thereprocase/5680-dock/desk-dock/D8/quick-fit/R5/README.md

# D8 R5: R4 plus a tall underside rail

**18 September 2026.** The printed R4-C pair carried the laptop, but a nudge
tipped it away from the lid rail: the 15-mm short fence cannot hold a 240-mm
lever pivoting on the seat, and the 5-degree lean gives only about 10 mm of
centre-of-gravity margin. R5 raises that fence into a 6-mm underside rail on the **plug-end bracket only**, 64 mm above the seat datum (unleaned z 47..118), keeping
the R2 lower profile, the 2.25-mm running clearance and a 4 x 2 mm lead-in at
the top. The laptop docks along -X from an 18-mm undocked offset, so the rear
rubber-foot strip (x 30..323 docked) sweeps x 30..341: it never reaches the
plug-end bracket (x < 18) but slides through the far-end bracket's x range, so
the far end keeps the R4-C profile without the wall. One wall stops the
rotation. The builder records the docking sweep and asserts the plug-end
clearance. Pair = one R5-C (plug end) + one R4-C (far end); the two R4-C
already printed cover the far end.

Tip receipt (variant C, nominal laptop rotated about the seat front edge toward
the underside side): 2° grazes the lead-in, 4° and beyond the rail carries it.
Everything else is R4: R2 seat, V5 lid-rail move, 6-mm rail, 6-mm base and
brace, fillets and chamfers. `--variant C --base-thickness 4 --tag d9-source`
exports the D9 P4 cradle profile.

Future idea (user, 18 September): make the seat, fence lower profile and
hinge relief a keyed insert so the same two walls and brace serve other
laptops; try a lean of 8 degrees on a bracket pair before changing the dock.
