thereprocase/5680-dock/desk-dock/D9-P5/asa-01-receipts/geometry-review.md

D9 P5 geometry-selected manufacturing review

P5: lean 8 degrees; each cradle end is the R7 frame with a drop-in seat peg
and fence peg locked by one horizontal fan pin (plate 08, 100 % infill,
profile on bed like the cradles). Plate 09 is the M1 cradle end sliced to its
16-mm frame width with the M1 pegs and pin: the cheap 8-degree seat trial,
same pose and profile as the cradle. The plenum, guard, tie and fastener plates
are P4. The lid rail is the only laptop-touching surface left on the frame.

P4 = P3 plus the R5-C underside rail on both outer cradles and three fit
corrections from the printed P2 fit plate: 8.4-mm pin bores (0.2-mm diametral
clearance), key barbs 7.2 mm wide (1.8 mm total interference through the
5.4-mm slot), T tongue 12.1 mm tall (0.6 mm lower). Plate 00 is regenerated so
the new clearances can be trialled before the large parts.

P3 = P2 with the cradle contact taken from the R4-C bracket profile (V5 C seat
relief, lid rail moved 3.5 mm outward, 4-mm base so feet stay coplanar) and a
printable cosmetic edge treatment: fillets on profile corners that run along
each part's print Z (perimeter-only, no overhang), a 0.8-mm chamfer on the
ties' top edges, nothing on bed edges, and every mating zone protected (air
cavity, fan seats, sockets, pin bores, key slots, T joints, guard bars,
laptop contact band). Pins, keys and coupons are byte-identical to P2.

Outer cradle sides: complete broad exterior X face on bed; cavity opens upward.
Inner halves: broad X side on bed; cavity opens upward. Circular fan aperture
opens progressively toward its centre in this orientation. Supports under the
three seam tabs and blind fan sockets are reachable before assembly.
No blanket rejection for downward-facing area is used.
Guards: broad exterior face on bed, bars and spacer towers grow upwards.
Male T ties: broad top on bed; female ties: broad base on bed. The floor-backed
T shoulders carry longitudinal loads. The transverse pin prevents lifting.
Pins: octagonal longitudinal flat on bed; long axes and tension loads in layers.
Keys: broad flat on bed, locking leaves bend in XY. Printed keys are replaceable.
The 8.8-mm transverse bores have two-ended bridge landings and open access.
The selected shell/end-side orientation keeps supported undersides away from
the broad cosmetic outer side. Bed texture is intentional on those faces.
Five walls, six top/bottom layers and 40% gyroid are prototype settings.
Physical contact, load capacity and cooling are untested.
