thereprocase/5680-dock/desk-dock/concept.png

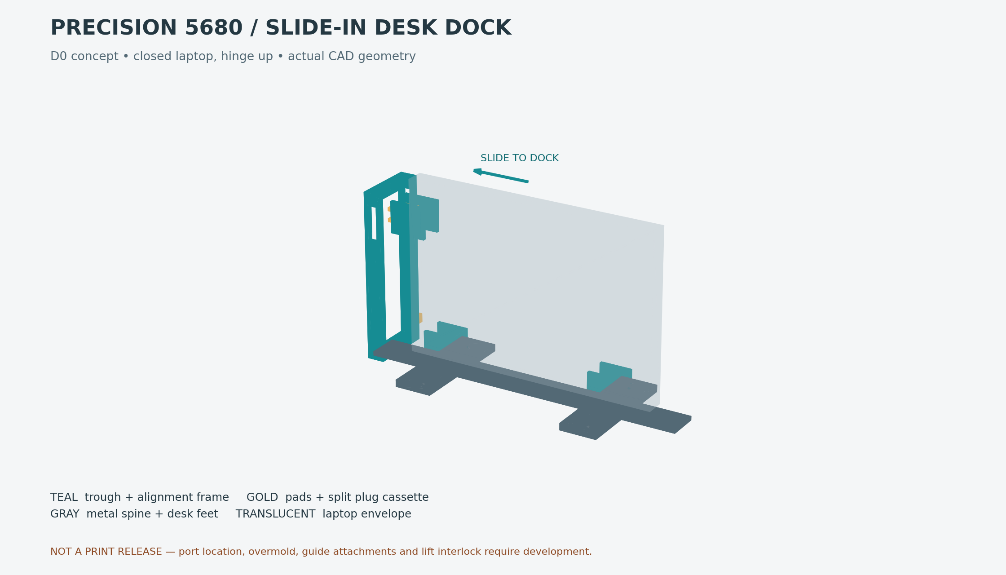
desk-dock/concept.png
