thereprocase/5680-dock/desk-dock/D2/overview.png

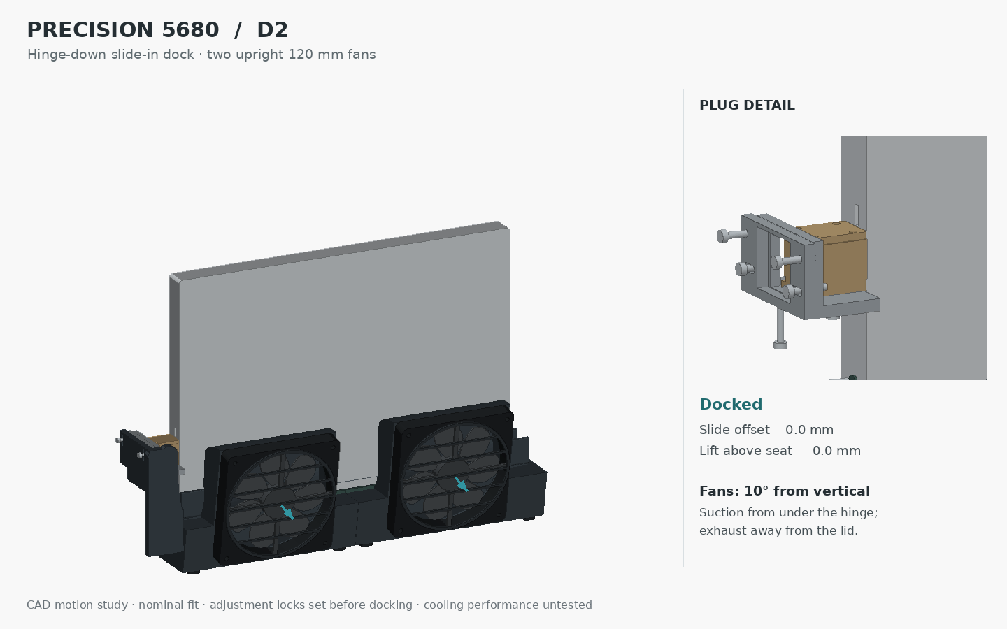
desk-dock/D2/overview.png
