thereprocase/5680-dock/desk-dock/D3/overview.png

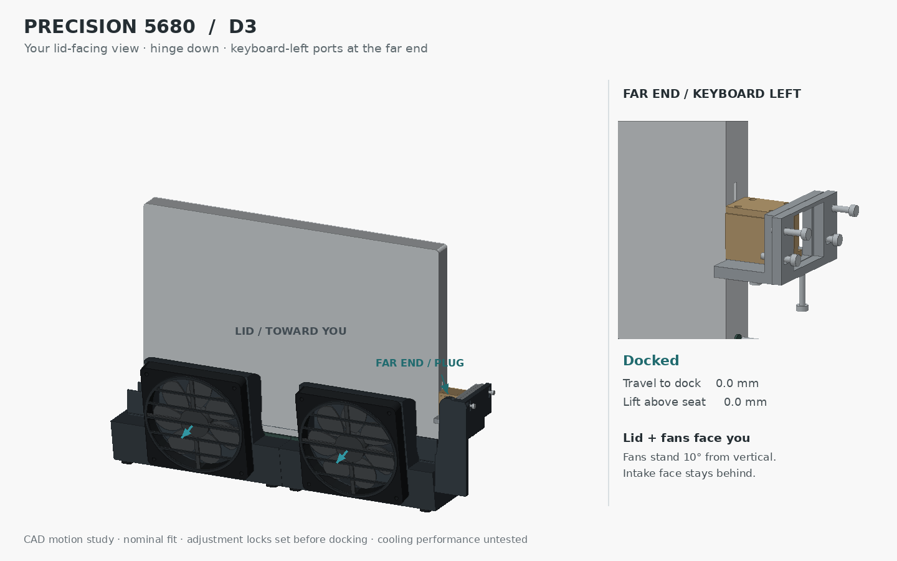
desk-dock/D3/overview.png
