thereprocase/5680-dock/desk-dock/D4/docking-cycle.gif

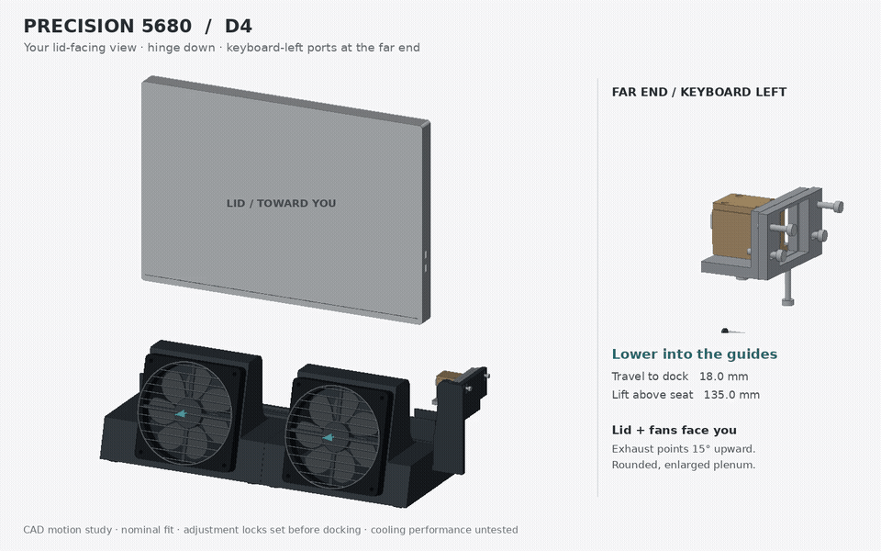
desk-dock/D4/docking-cycle.gif
