thereprocase/5680-dock/desk-dock/D5/docking-cycle.gif

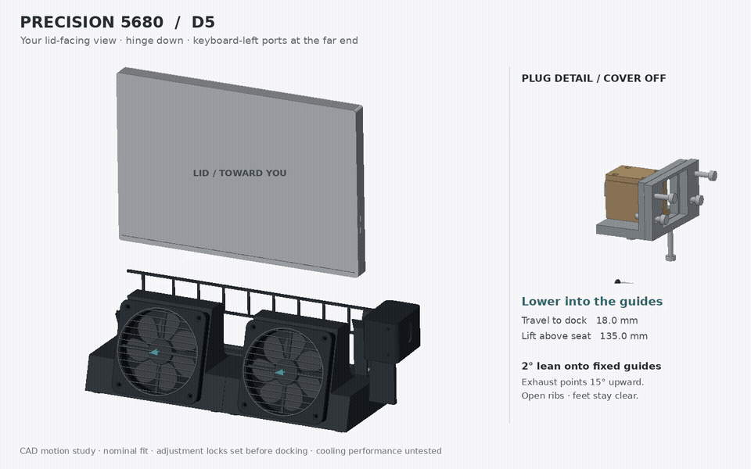
desk-dock/D5/docking-cycle.gif
