thereprocase/5680-dock/desk-dock/D5/profile-detail.png

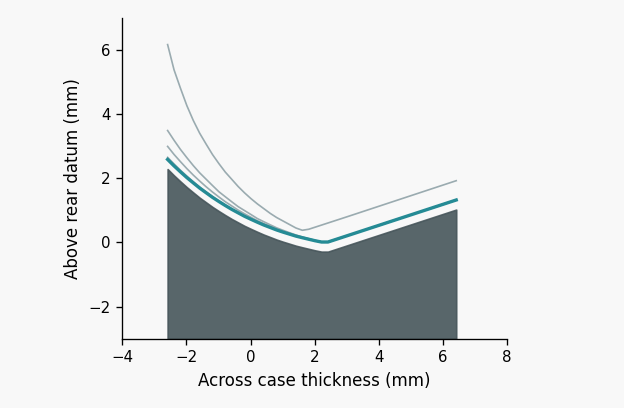
desk-dock/D5/profile-detail.png
