thereprocase/5680-dock/desk-dock/D6/contact-study.png

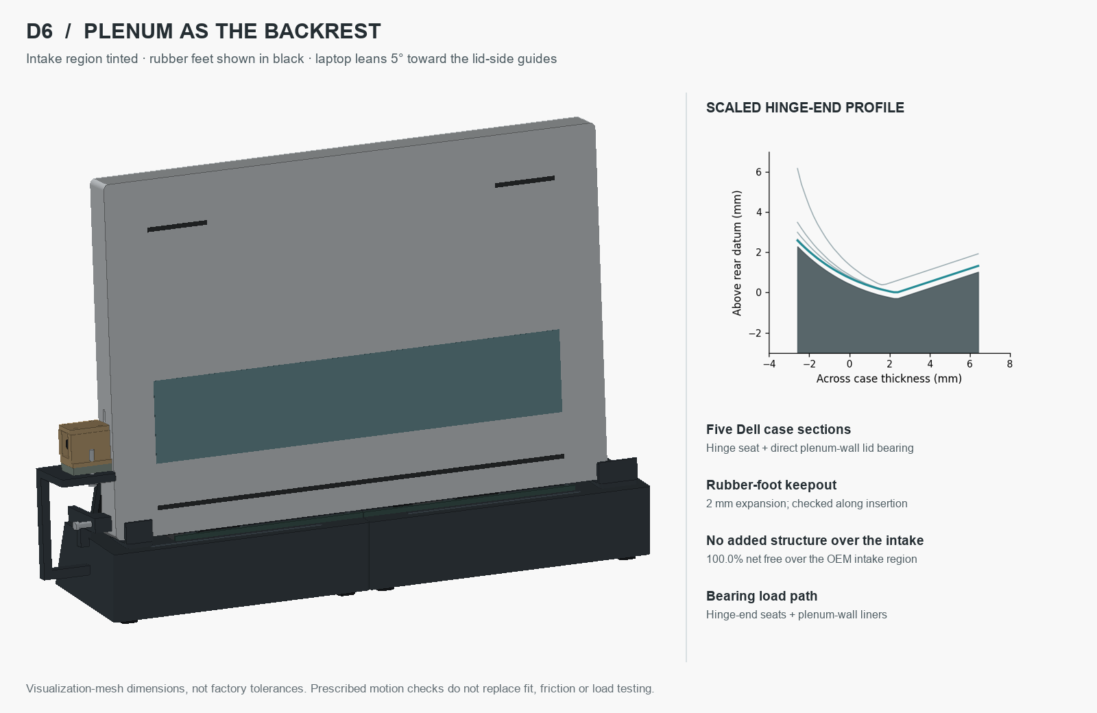
desk-dock/D6/contact-study.png
