thereprocase/5680-dock/desk-dock/D6/docking-cycle.gif

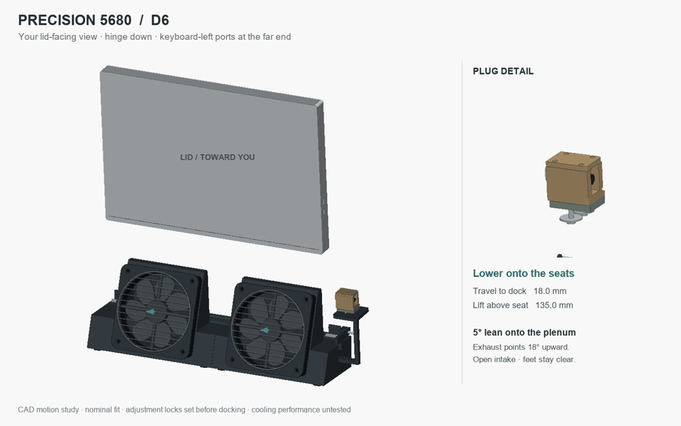
desk-dock/D6/docking-cycle.gif
