thereprocase/5680-dock/desk-dock/D7/D7-breakaway.png

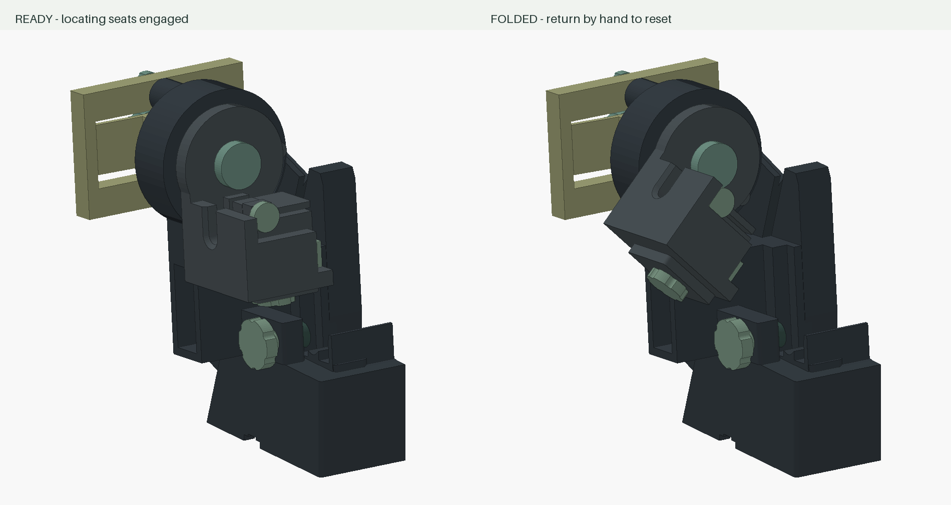
desk-dock/D7/D7-breakaway.png
