thereprocase/5680-dock/desk-dock/D7/D7-continuous-lip.png

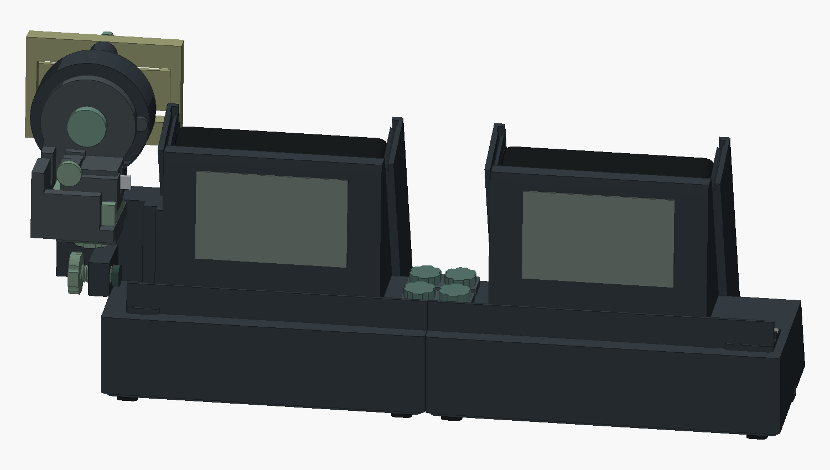
desk-dock/D7/D7-continuous-lip.png
