thereprocase/5680-dock/desk-dock/D7/D7-fan-pockets.png

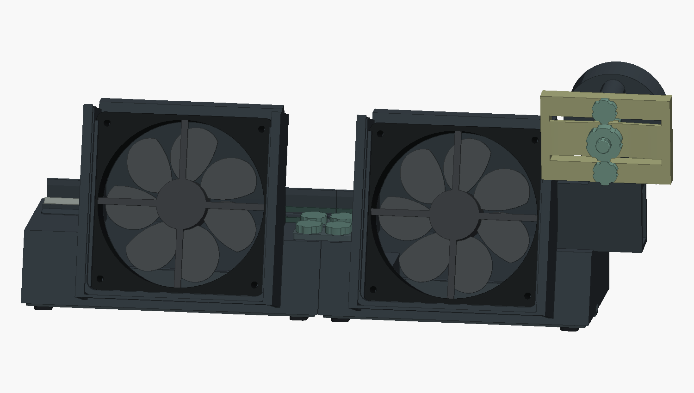
desk-dock/D7/D7-fan-pockets.png
