thereprocase/5680-dock/desk-dock/D8/D8-connector.png

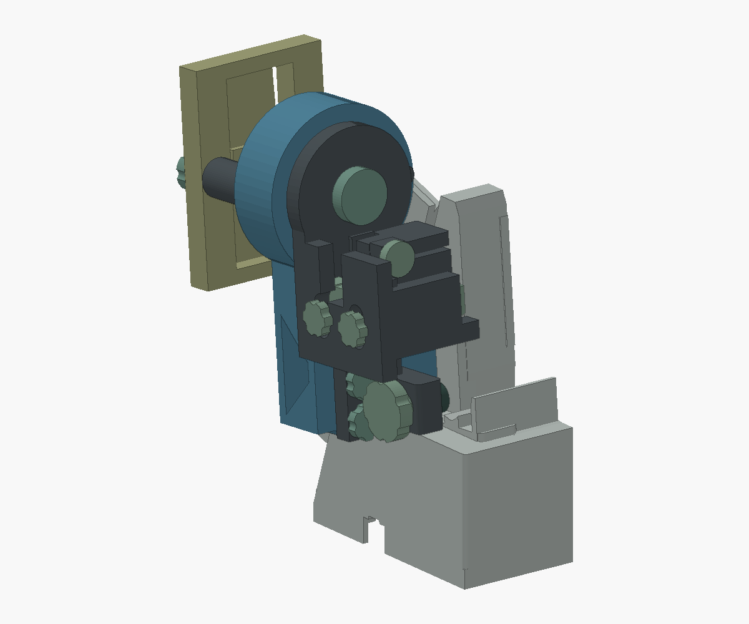
desk-dock/D8/D8-connector.png
