thereprocase/5680-dock/desk-dock/D8/D8-service-covers.png

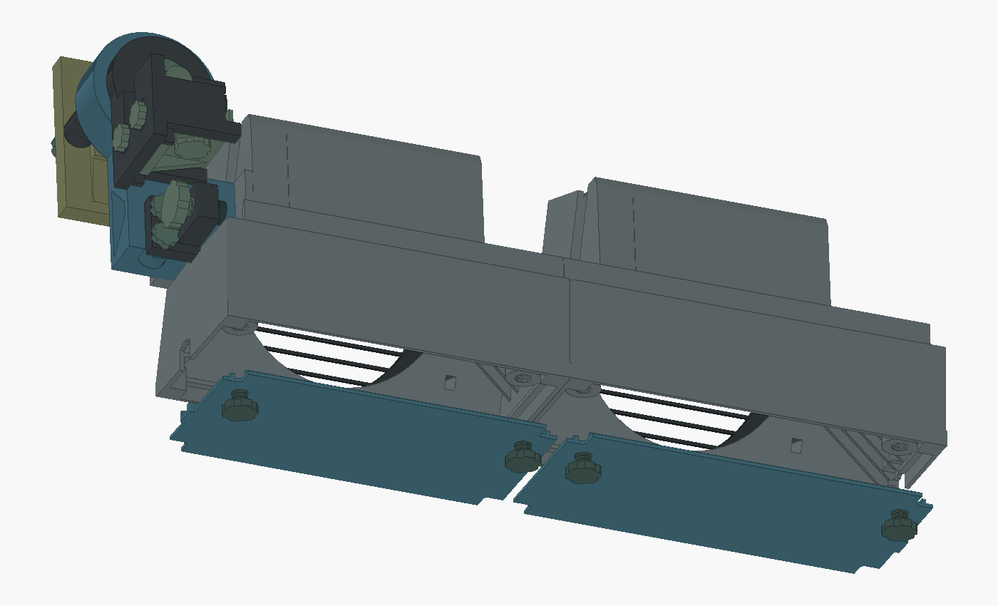
desk-dock/D8/D8-service-covers.png
