thereprocase/5680-dock/desk-dock/D8/quick-fit/R4/D8-R4-A-quick-fit-profile.png

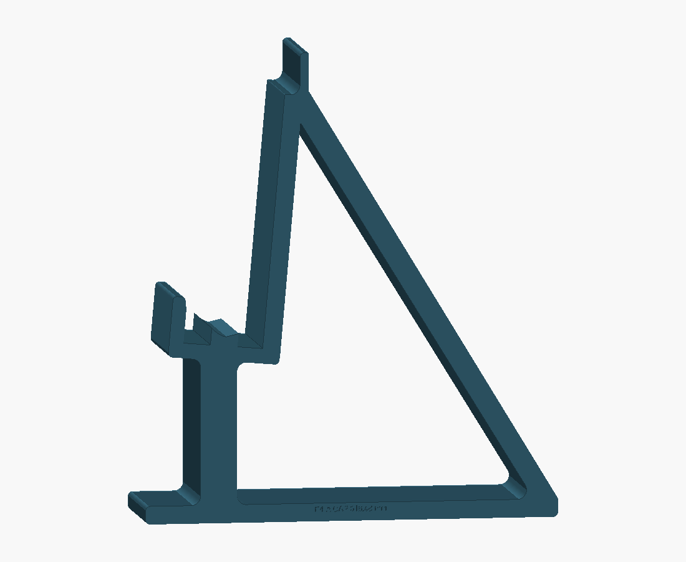
desk-dock/D8/quick-fit/R4/D8-R4-A-quick-fit-profile.png
