thereprocase/5680-dock/desk-dock/D8/quick-fit/R5/D8-R5-C-d9-source-quick-fit.png

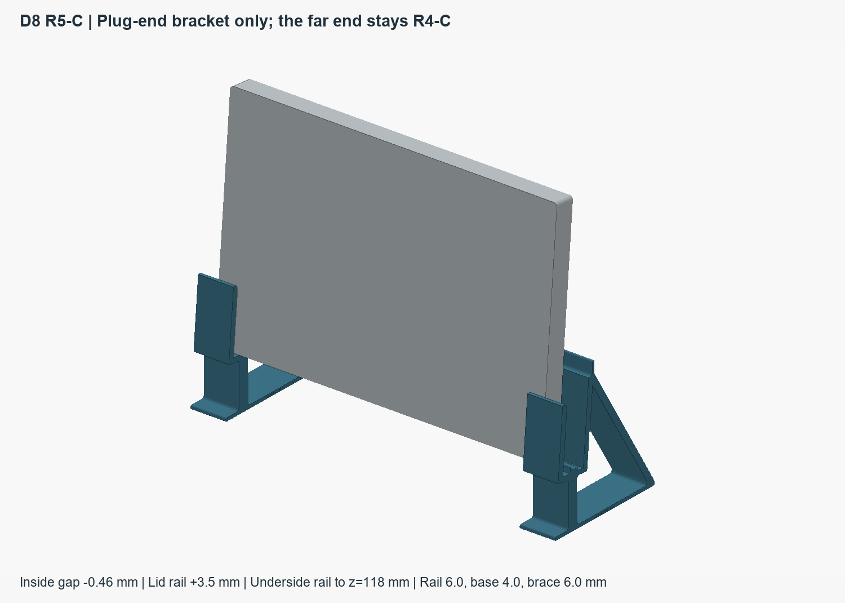
desk-dock/D8/quick-fit/R5/D8-R5-C-d9-source-quick-fit.png
