thereprocase/5680-dock/desk-dock/D8/quick-fit/R6/D8-R6-d9-source-profiles.png

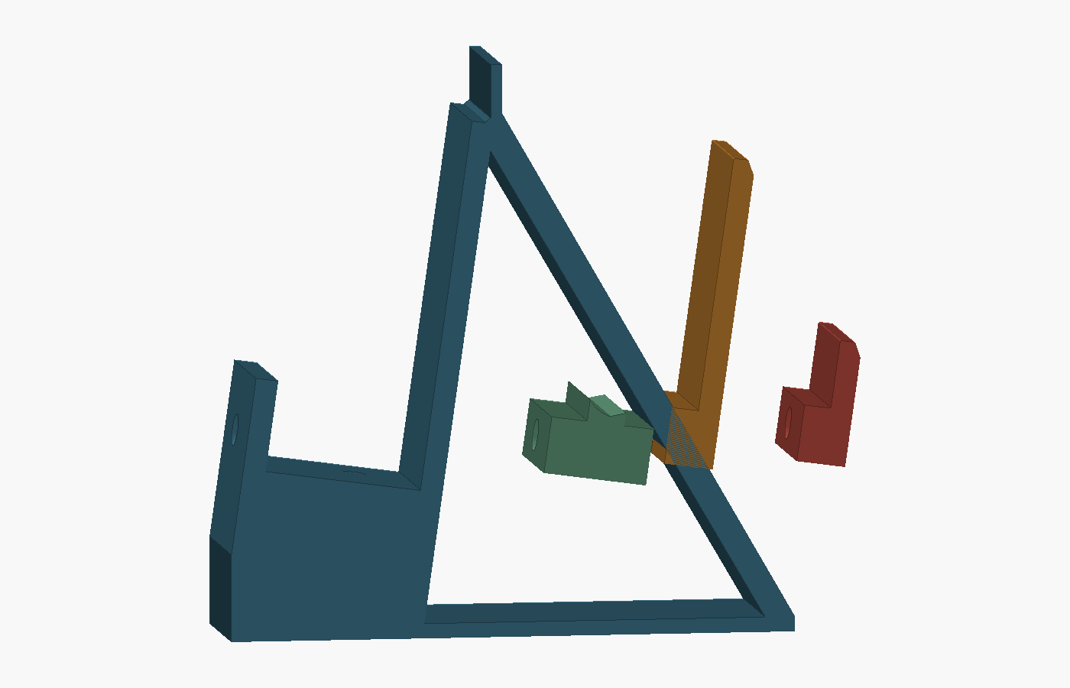
desk-dock/D8/quick-fit/R6/D8-R6-d9-source-profiles.png
