thereprocase/5680-dock/desk-dock/D8/quick-fit/R7/D8-R7-demo-T11-profiles.png

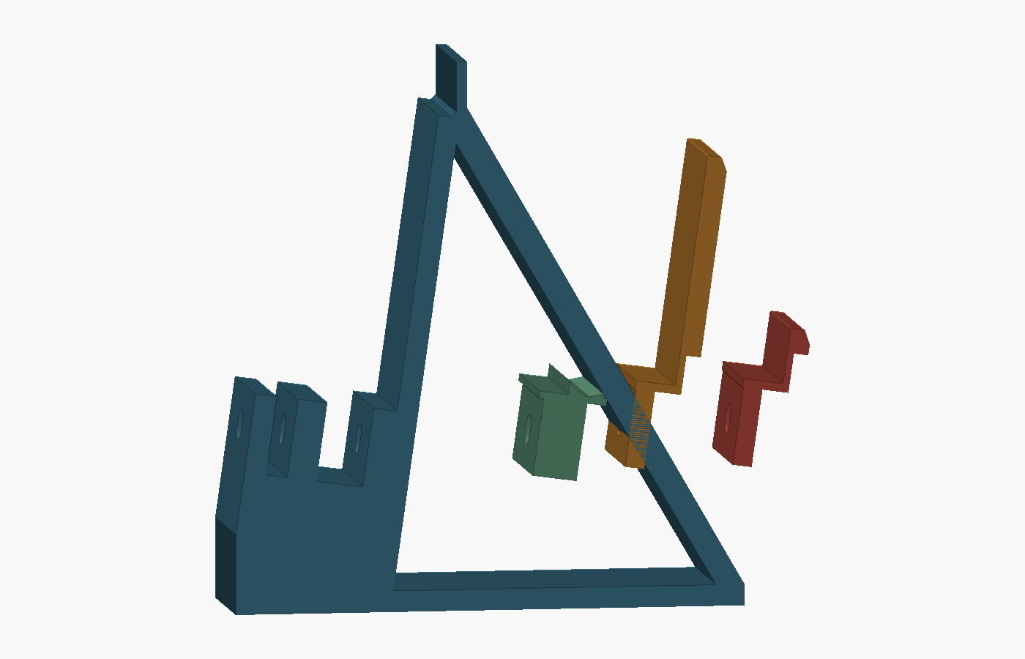
desk-dock/D8/quick-fit/R7/D8-R7-demo-T11-profiles.png
