thereprocase/5680-dock/desk-dock/D9-P5/asa-01-receipts/actual-toolpaths.png

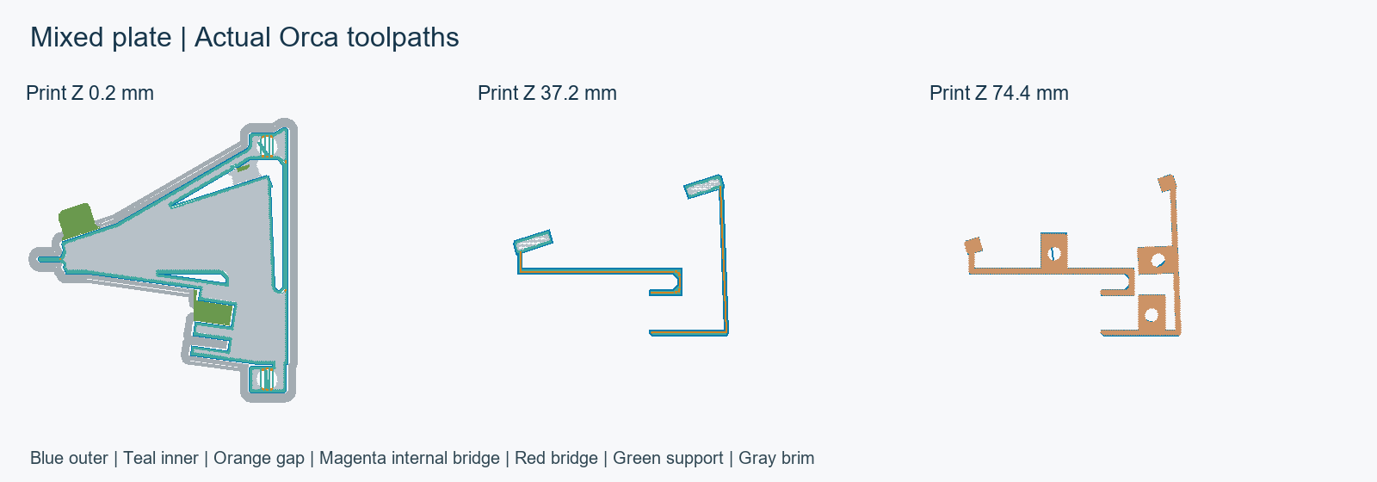
desk-dock/D9-P5/asa-01-receipts/actual-toolpaths.png
