thereprocase/5680-dock/desk-dock/D9-P5/audit/plug-end-views.png

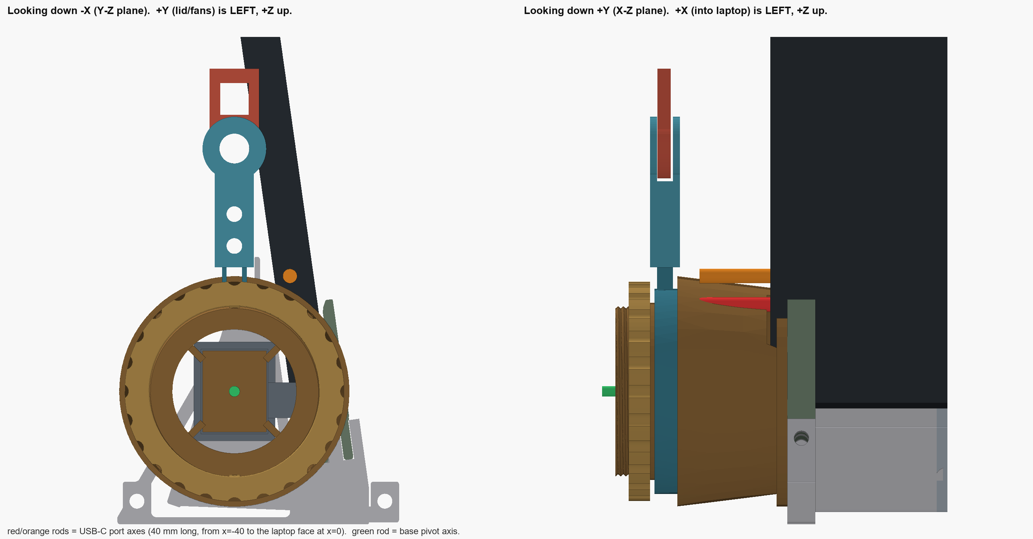
desk-dock/D9-P5/audit/plug-end-views.png
