thereprocase/5680-dock/desk-dock/D9-P5/audit/port-reach.png

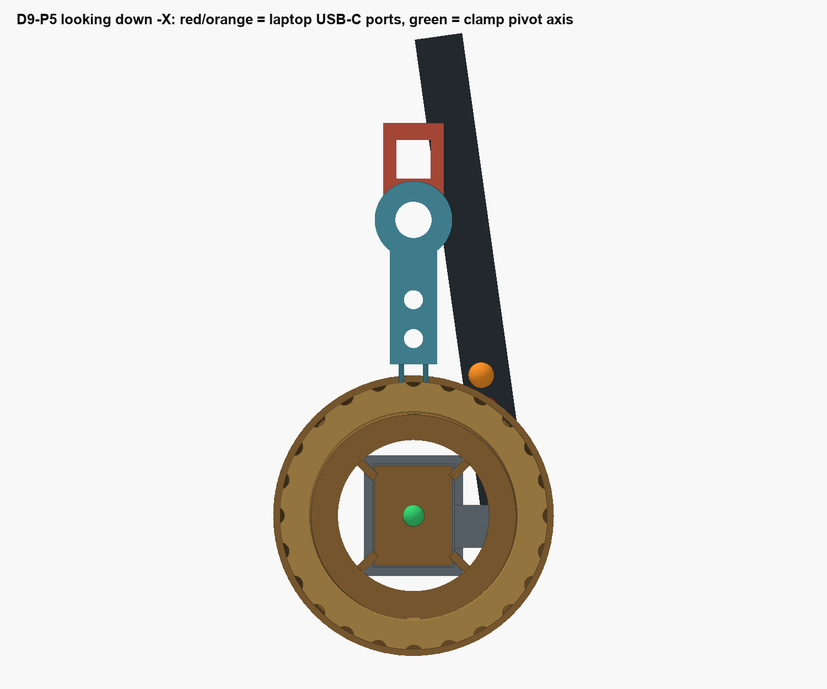
desk-dock/D9-P5/audit/port-reach.png
