thereprocase/5680-dock/desk-dock/D9-P5/clamp-pivot-views/03-exploded-clamp-stack.png

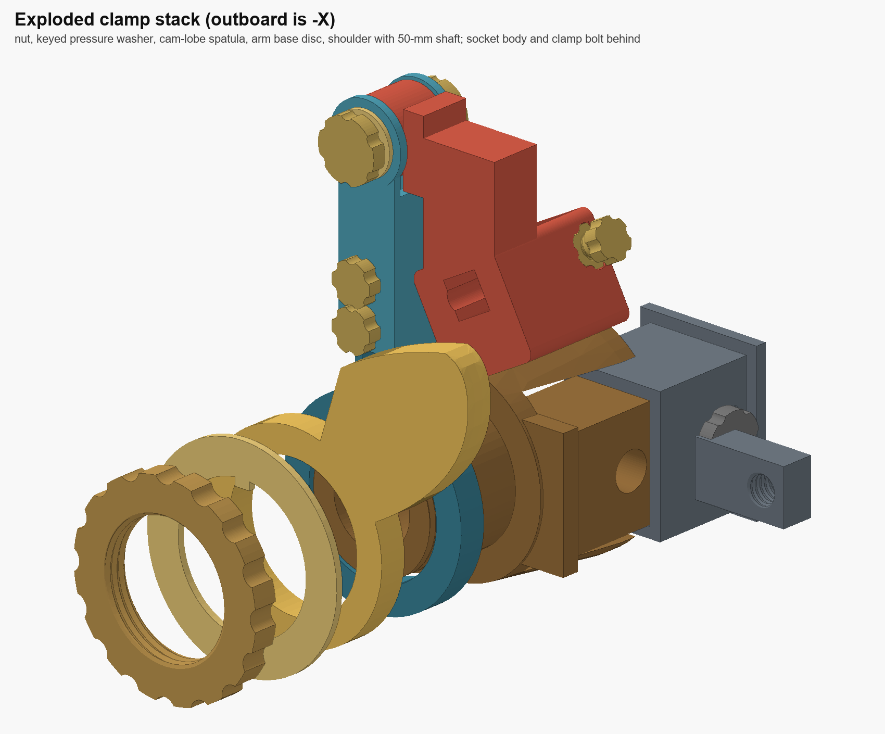
desk-dock/D9-P5/clamp-pivot-views/03-exploded-clamp-stack.png
