thereprocase/5680-dock/desk-dock/D9-P5/clamp-pivot-views/04-axial-section.png

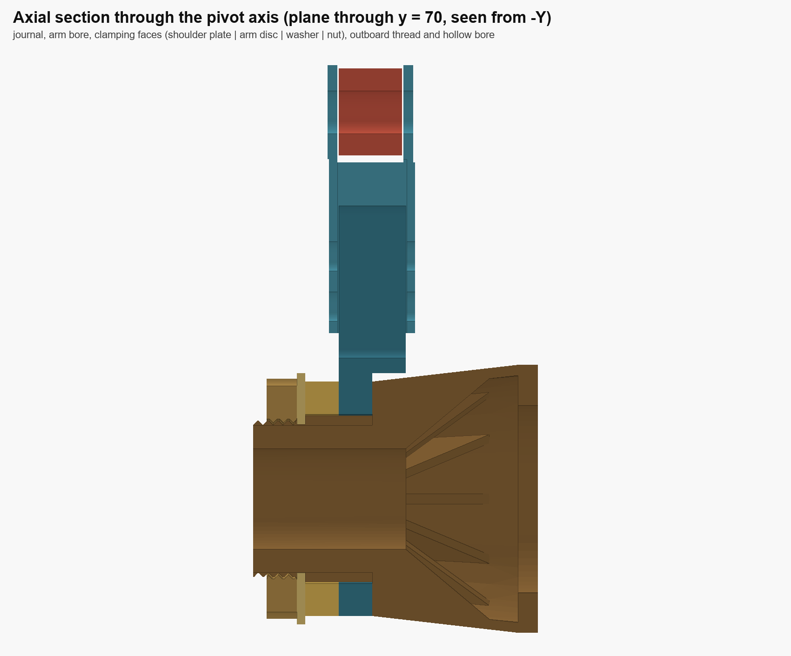
desk-dock/D9-P5/clamp-pivot-views/04-axial-section.png
