thereprocase/5680-dock/desk-dock/D9-P5/clamp-pivot-views/05-thread-closeup.png

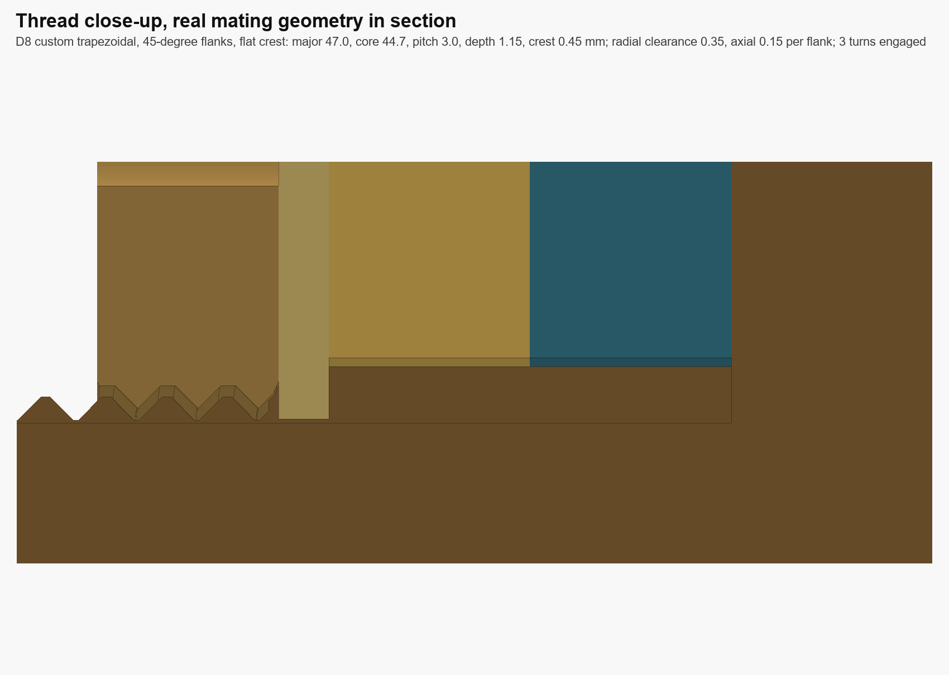
desk-dock/D9-P5/clamp-pivot-views/05-thread-closeup.png
