thereprocase/5680-dock/desk-dock/D9-P5/clamp-pivot-views/06-rotor-at-port.png

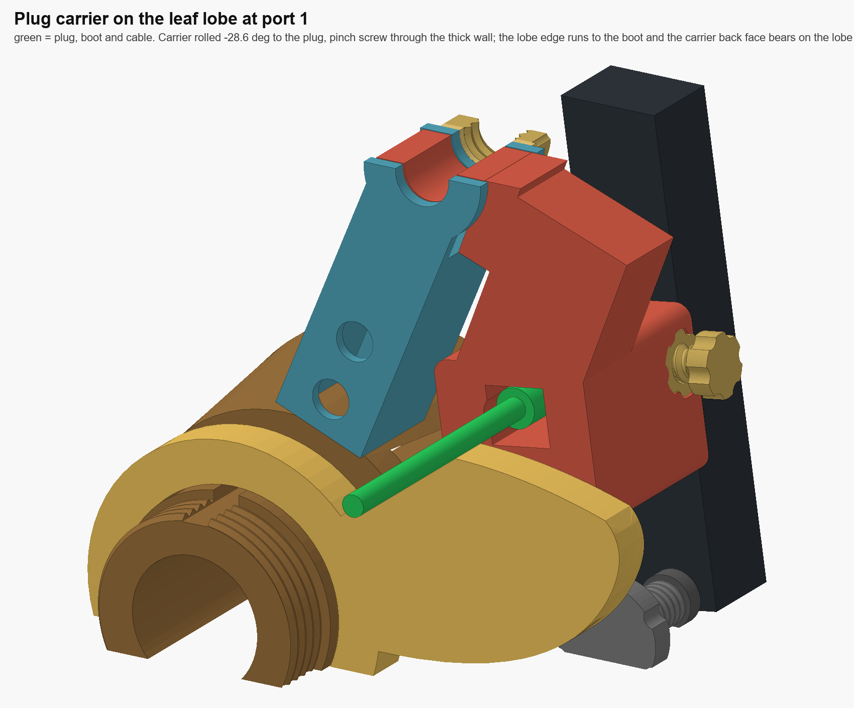
desk-dock/D9-P5/clamp-pivot-views/06-rotor-at-port.png
