thereprocase/5680-dock/desk-dock/D9-P5/clamp-pivot-views/07-lobe-and-tunnel-end-view.png

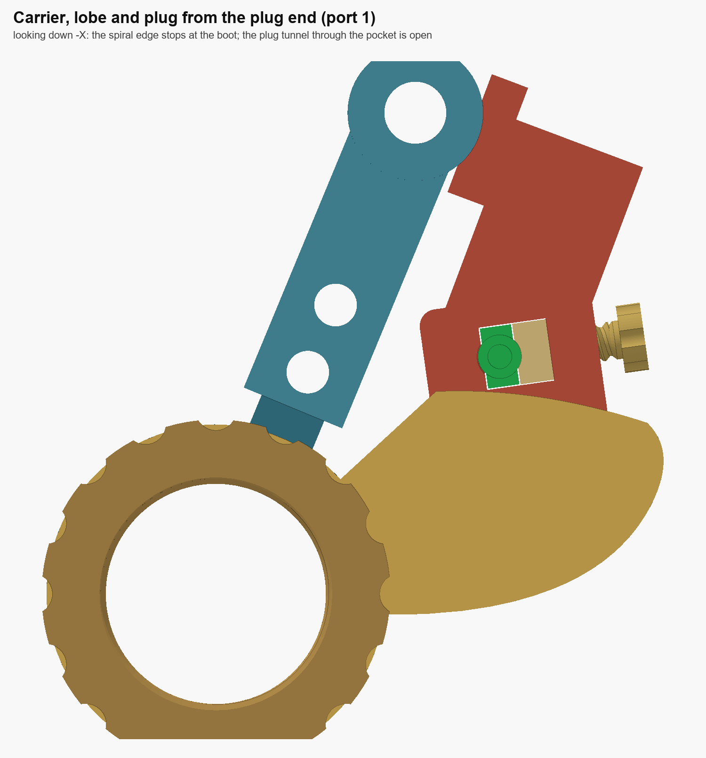
desk-dock/D9-P5/clamp-pivot-views/07-lobe-and-tunnel-end-view.png
