thereprocase/5680-dock/desk-dock/D9-P5/clamp-pivot-views/08-window-section.png

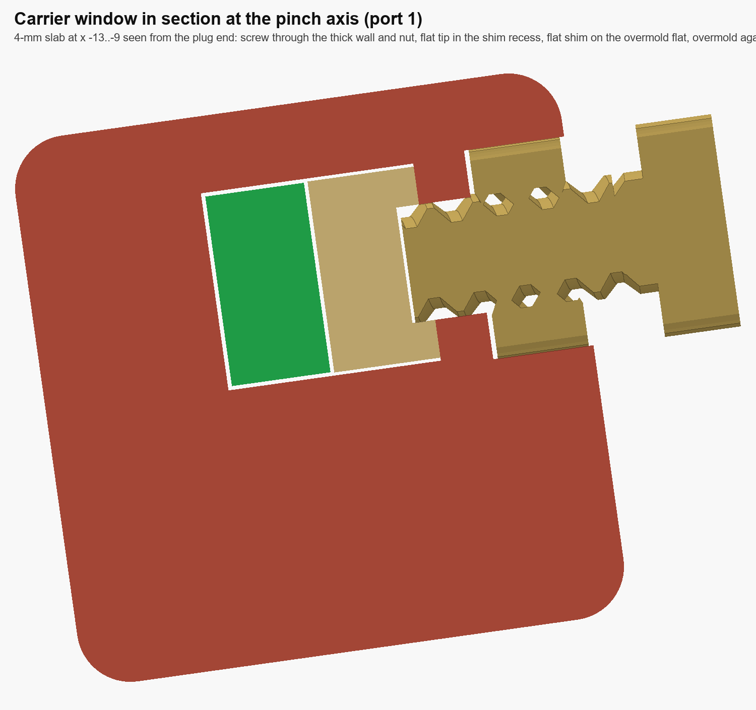
desk-dock/D9-P5/clamp-pivot-views/08-window-section.png
