thereprocase/5680-dock/desk-dock/D9-P5/splice-outlines.png

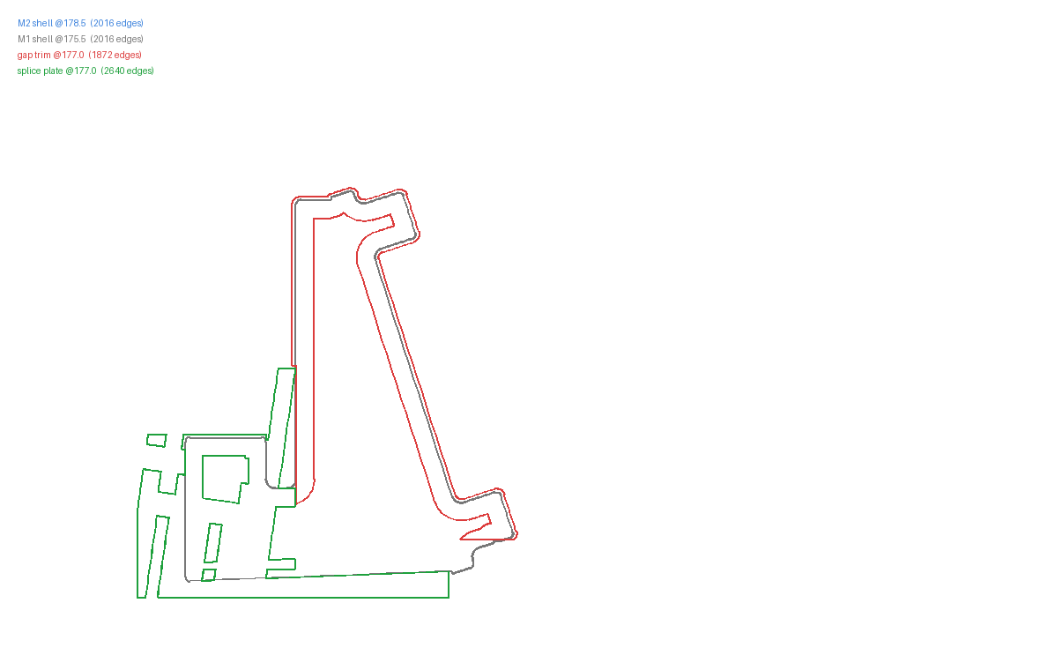
desk-dock/D9-P5/splice-outlines.png
