thereprocase/5680-dock/desk-dock/D7/print-review/02_bottom_panel/plate.stl

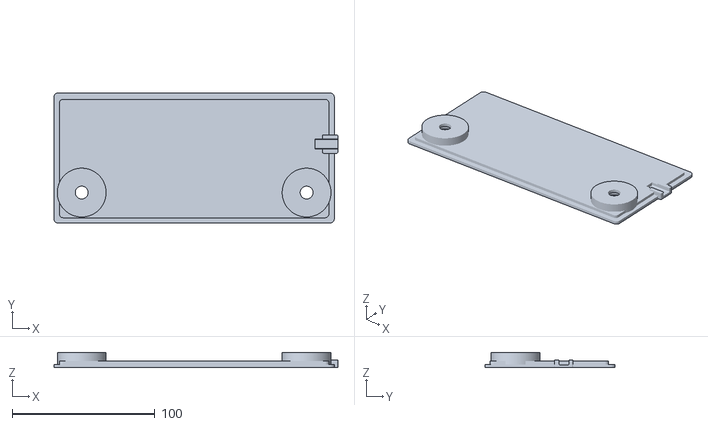
[picture p111: CAD file, 2026-10-06]
desk-dock/D7/print-review/02_bottom_panel/plate.stl
198.9 x 91.2 x 10.7
