thereprocase/5680-dock/desk-dock/D7/print-review/02_manifold_with_cradle/plate.stl

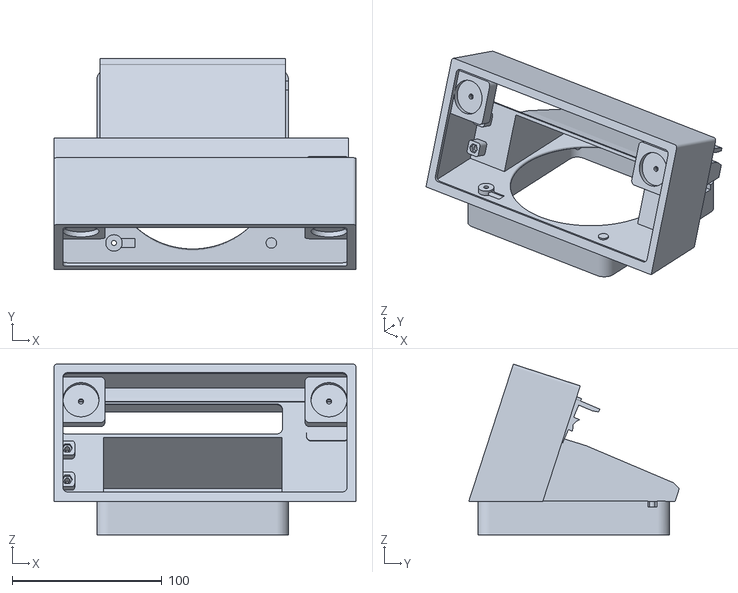
[picture p112: CAD file, 2026-10-06]
desk-dock/D7/print-review/02_manifold_with_cradle/plate.stl
201.5 x 140.6 x 114.0
