thereprocase/5680-dock/desk-dock/D7/print-review/breakaway_carrier/plate.stl

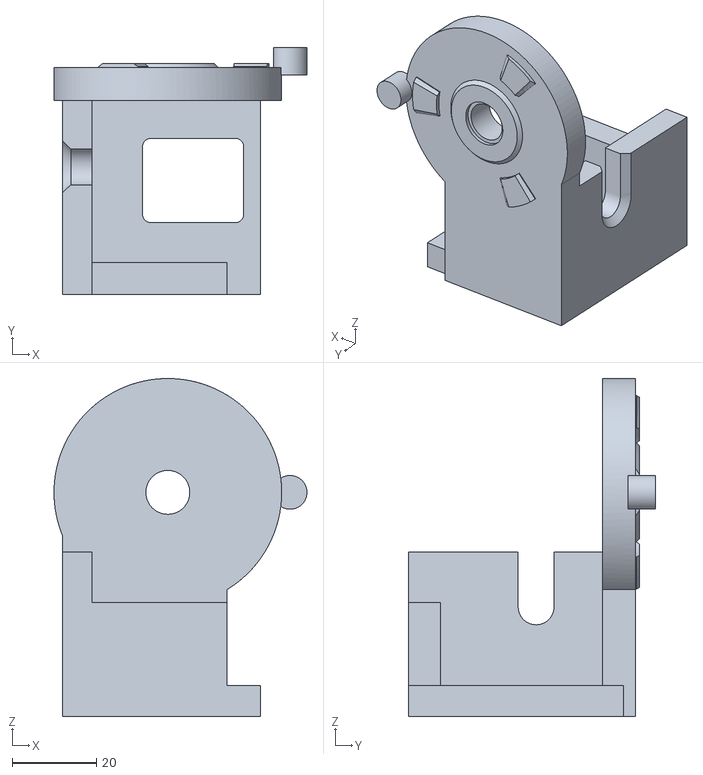
[picture p113: CAD file, 2026-10-06]
desk-dock/D7/print-review/breakaway_carrier/plate.stl
60.0 x 58.5 x 80.1
