thereprocase/5680-dock/desk-dock/D7/print-review/breakaway_pivot_pin_10mm/plate.stl

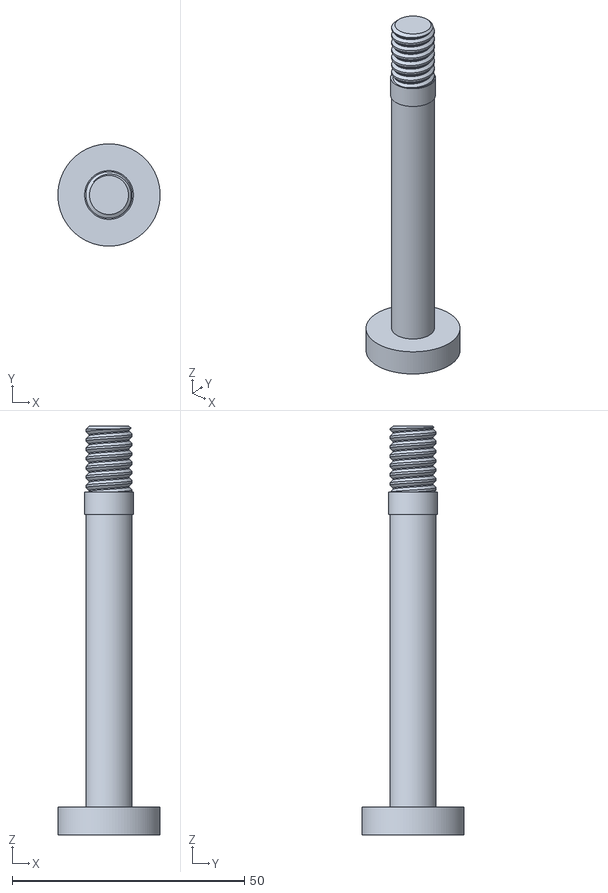
[picture p114: CAD file, 2026-10-06]
desk-dock/D7/print-review/breakaway_pivot_pin_10mm/plate.stl
22.0 x 22.0 x 88.0
