thereprocase/5680-dock/desk-dock/D7/print-review/breakaway_preload_hand_nut/plate.stl

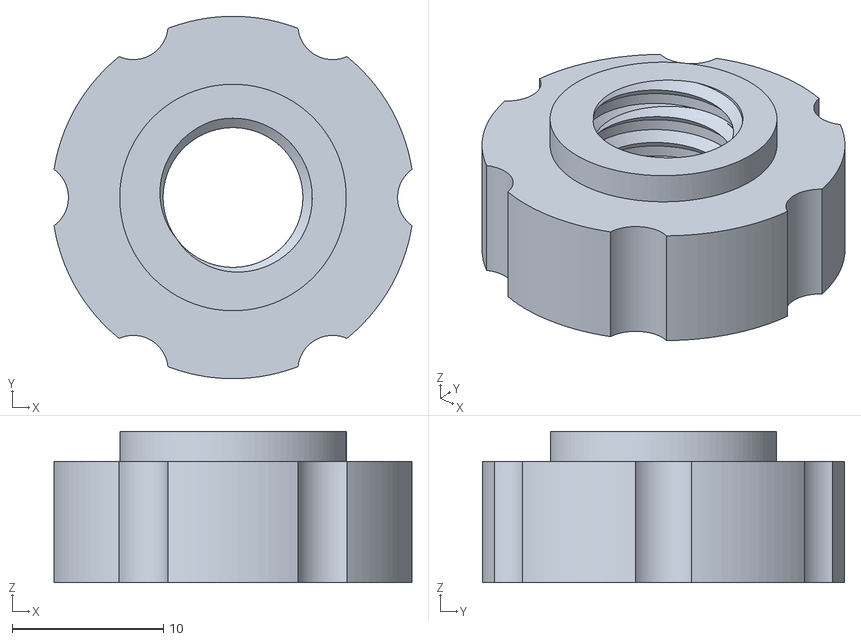
[picture p115: CAD file, 2026-10-06]
desk-dock/D7/print-review/breakaway_preload_hand_nut/plate.stl
23.7 x 24.0 x 10.0
