thereprocase/5680-dock/desk-dock/D7/print-review/breakaway_spring_cartridge/plate.stl

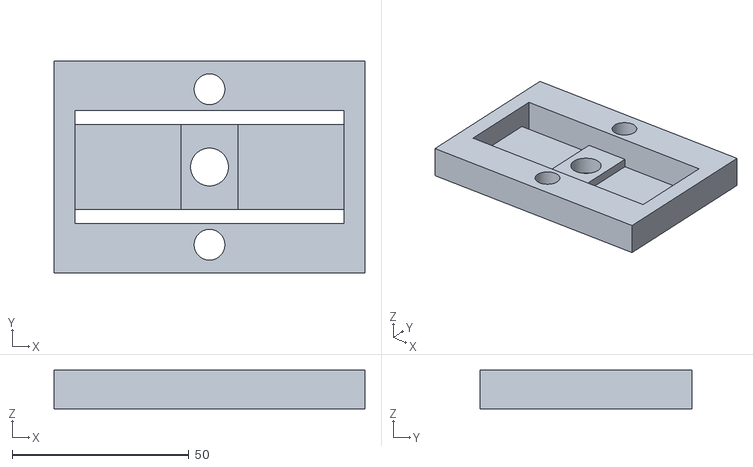
[picture p116: CAD file, 2026-10-06]
desk-dock/D7/print-review/breakaway_spring_cartridge/plate.stl
88.0 x 60.0 x 11.0
