thereprocase/5680-dock/desk-dock/D7/print-review/bridge_key_1/plate.stl

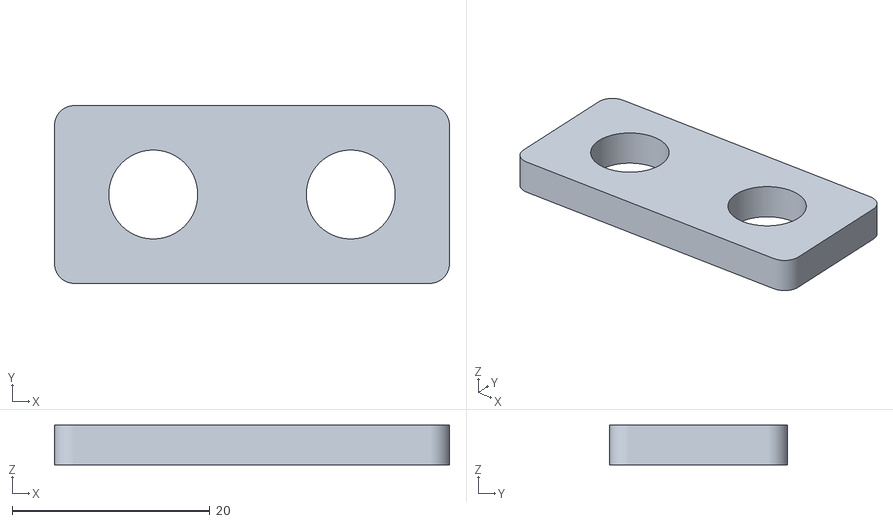
[picture p117: CAD file, 2026-10-06]
desk-dock/D7/print-review/bridge_key_1/plate.stl
40.0 x 18.0 x 4.00
