thereprocase/5680-dock/desk-dock/D7/print-review/cassette_calibration_keeper_plate/plate.stl

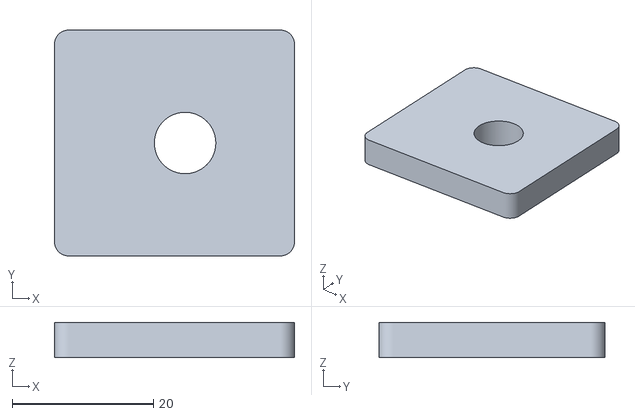
[picture p118: CAD file, 2026-10-06]
desk-dock/D7/print-review/cassette_calibration_keeper_plate/plate.stl
34.0 x 32.0 x 5.00
