thereprocase/5680-dock/desk-dock/D7/print-review/cassette_cap_push_pin_6p5/plate.stl

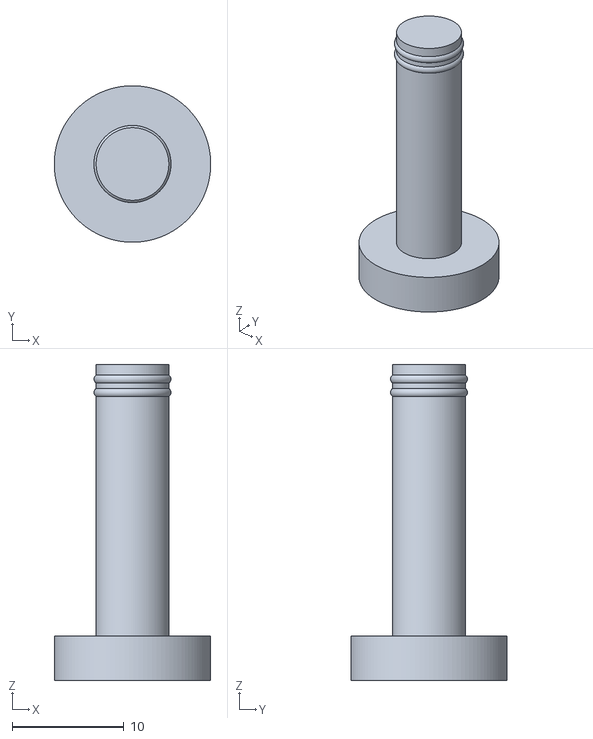
[picture p119: CAD file, 2026-10-06]
desk-dock/D7/print-review/cassette_cap_push_pin_6p5/plate.stl
14.0 x 14.0 x 28.3
