thereprocase/5680-dock/desk-dock/D7/print-review/cassette_thumb_knob_-8.0/plate.stl

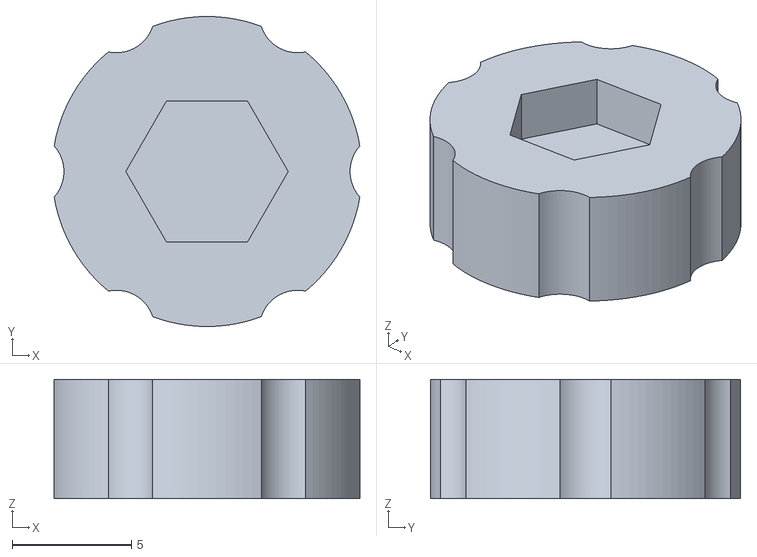
[picture p120: CAD file, 2026-10-06]
desk-dock/D7/print-review/cassette_thumb_knob_-8.0/plate.stl
12.8 x 13.0 x 5.00
