thereprocase/5680-dock/desk-dock/D7/print-review/COUPON_bottom_socket_gap_0p35_per_side_R3/plate.stl

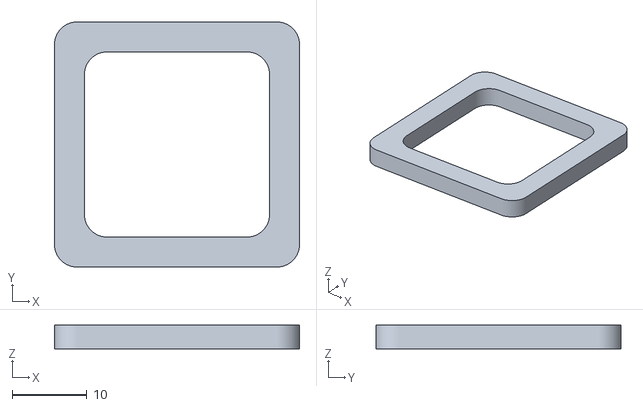
[picture p121: CAD file, 2026-10-06]
desk-dock/D7/print-review/COUPON_bottom_socket_gap_0p35_per_side_R3/plate.stl
32.7 x 32.7 x 3.20
