thereprocase/5680-dock/desk-dock/D7/print-review/COUPON_bottom_tongue_male_R2p65/plate.stl

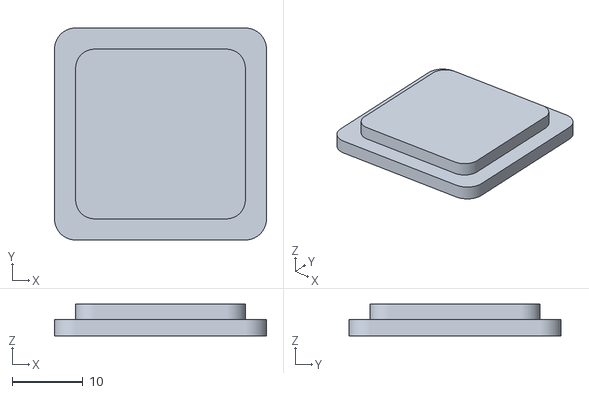
[picture p122: CAD file, 2026-10-06]
desk-dock/D7/print-review/COUPON_bottom_tongue_male_R2p65/plate.stl
30.0 x 30.0 x 4.50
