thereprocase/5680-dock/desk-dock/D7/print-review/coupon_cap_pin_receiver_bore_6.8/plate.stl

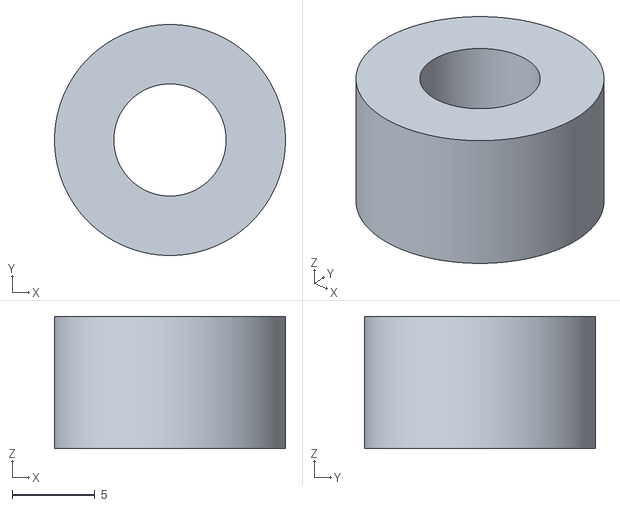
[picture p123: CAD file, 2026-10-06]
desk-dock/D7/print-review/coupon_cap_pin_receiver_bore_6.8/plate.stl
14.0 x 14.0 x 8.00
