thereprocase/5680-dock/desk-dock/D7/print-review/COUPON_cap_T_female_gap_0p20_per_side/plate.stl

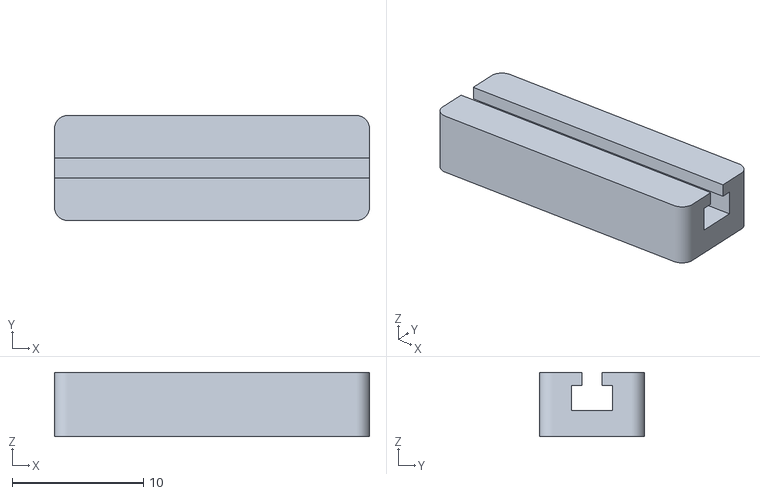
[picture p124: CAD file, 2026-10-06]
desk-dock/D7/print-review/COUPON_cap_T_female_gap_0p20_per_side/plate.stl
24.0 x 8.00 x 4.90
