thereprocase/5680-dock/desk-dock/D7/print-review/COUPON_cap_T_male_2p7_head_1p1_neck/plate.stl

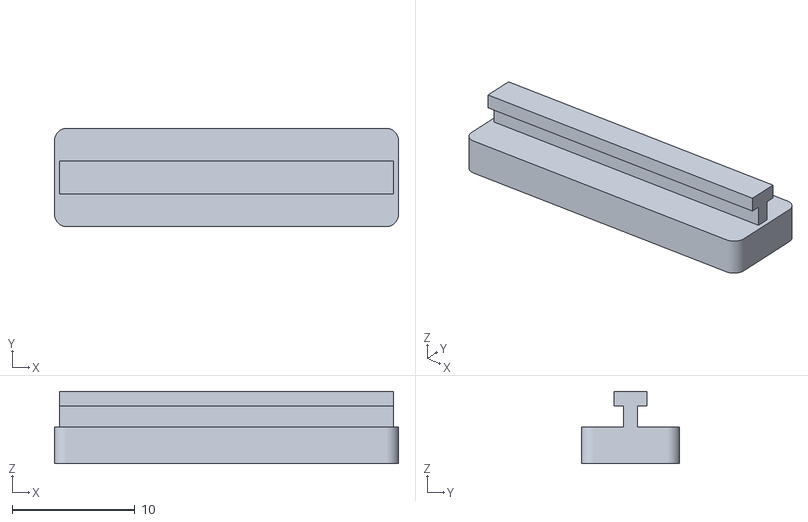
[picture p125: CAD file, 2026-10-06]
desk-dock/D7/print-review/COUPON_cap_T_male_2p7_head_1p1_neck/plate.stl
28.0 x 8.00 x 5.90
