thereprocase/5680-dock/desk-dock/D7/print-review/coupon_dummy_plug_load_eye/plate.stl

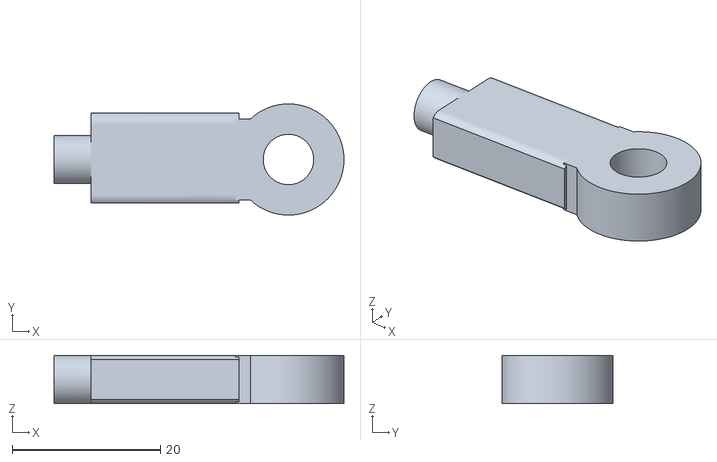
[picture p126: CAD file, 2026-10-06]
desk-dock/D7/print-review/coupon_dummy_plug_load_eye/plate.stl
39.1 x 15.0 x 6.50
