thereprocase/5680-dock/desk-dock/D7/print-review/coupon_fan_grille_edge/plate.stl

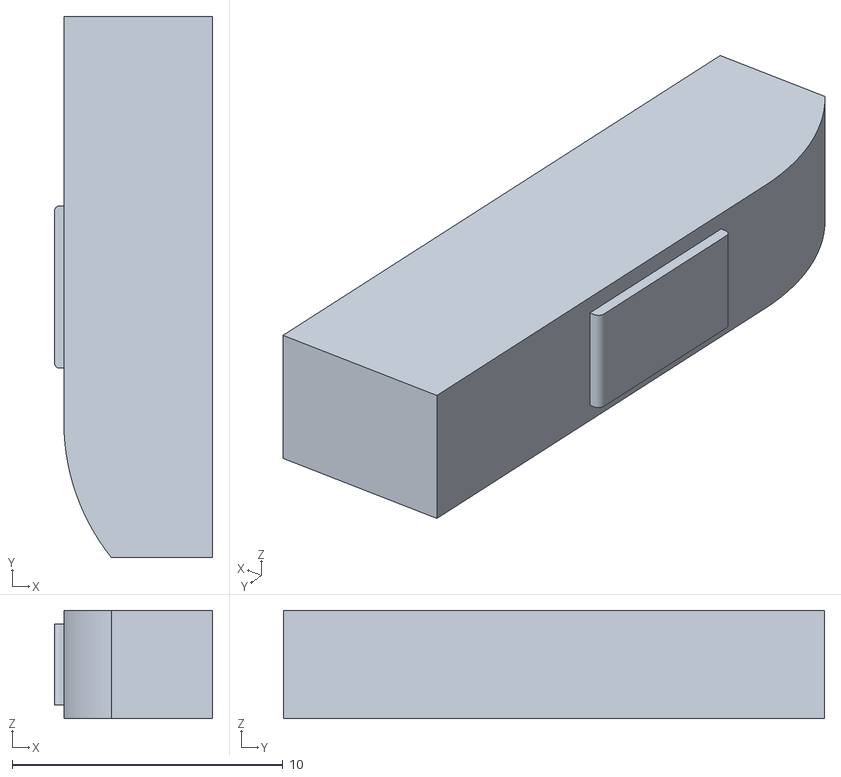
[picture p127: CAD file, 2026-10-06]
desk-dock/D7/print-review/coupon_fan_grille_edge/plate.stl
5.85 x 20.0 x 4.00
