thereprocase/5680-dock/desk-dock/D7/print-review/COUPON_fan_rim_corner_gap_0p50_per_side/plate.stl

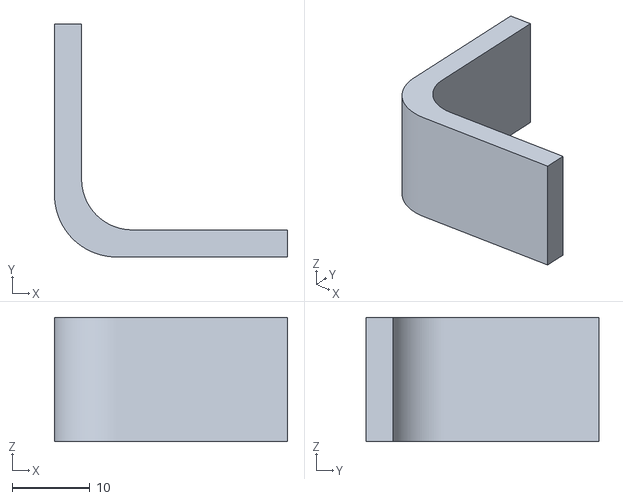
[picture p128: CAD file, 2026-10-06]
desk-dock/D7/print-review/COUPON_fan_rim_corner_gap_0p50_per_side/plate.stl
30.0 x 30.0 x 16.0
