thereprocase/5680-dock/desk-dock/D7/print-review/coupon_fan_slide_rail/plate.stl

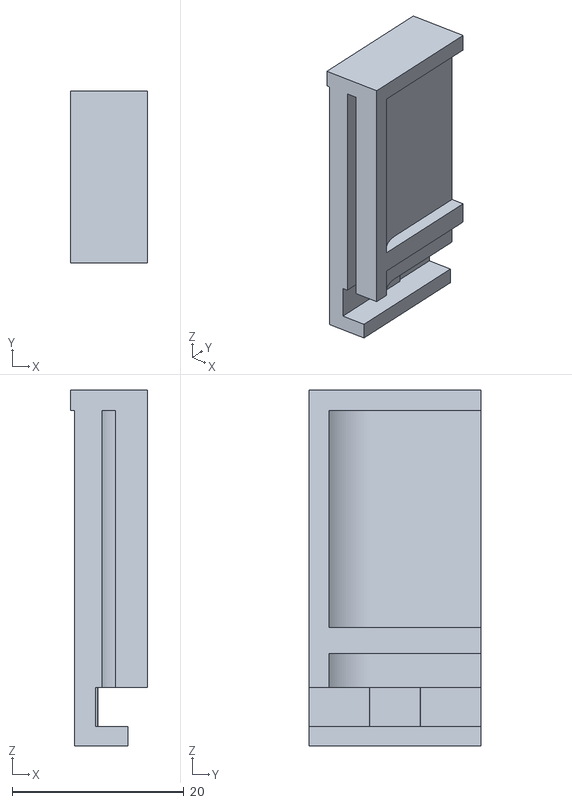
[picture p129: CAD file, 2026-10-06]
desk-dock/D7/print-review/coupon_fan_slide_rail/plate.stl
9.00 x 20.0 x 41.5
