thereprocase/5680-dock/desk-dock/D7/print-review/coupon_fixed_cam_and_pilot/plate.stl

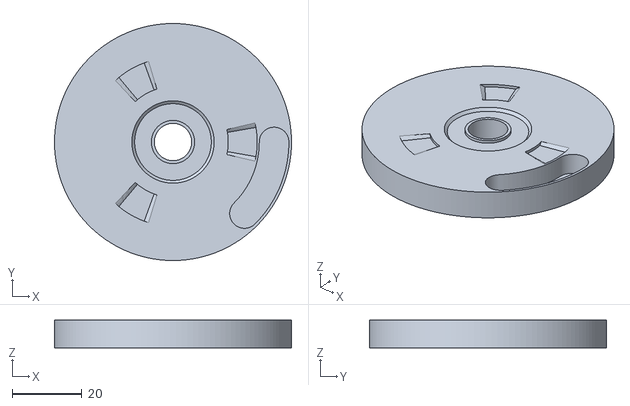
[picture p130: CAD file, 2026-10-06]
desk-dock/D7/print-review/coupon_fixed_cam_and_pilot/plate.stl
68.0 x 68.0 x 8.00
