thereprocase/5680-dock/desk-dock/D7/print-review/COUPON_M3_hex_AF_5p7_5p9_6p1_left_to_right/plate.stl

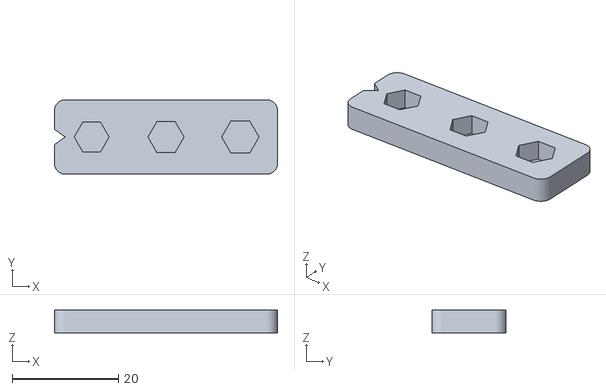
[picture p131: CAD file, 2026-10-06]
desk-dock/D7/print-review/COUPON_M3_hex_AF_5p7_5p9_6p1_left_to_right/plate.stl
42.0 x 14.0 x 4.25
