thereprocase/5680-dock/desk-dock/D7/print-review/coupon_rotor_cam_and_pilot/plate.stl

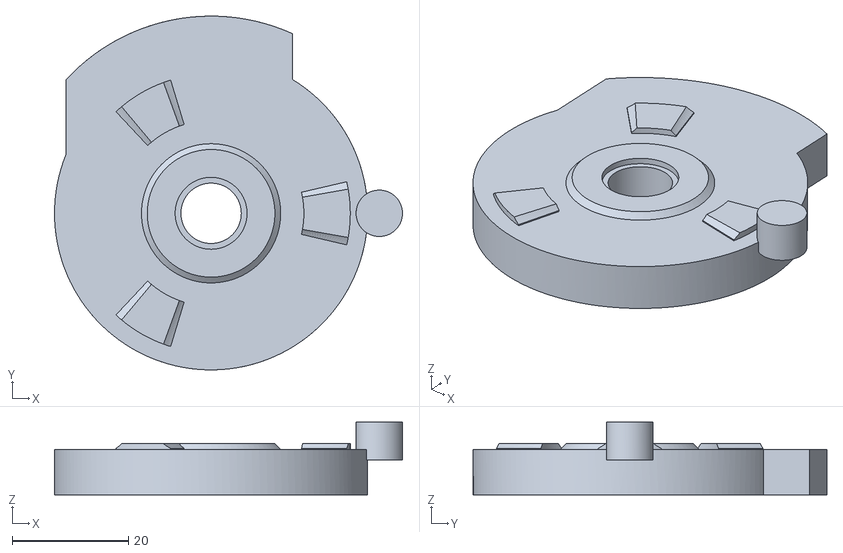
[picture p132: CAD file, 2026-10-06]
desk-dock/D7/print-review/coupon_rotor_cam_and_pilot/plate.stl
60.0 x 61.0 x 12.5
