thereprocase/5680-dock/desk-dock/D7/print-review/height_shim_pack/plate.stl

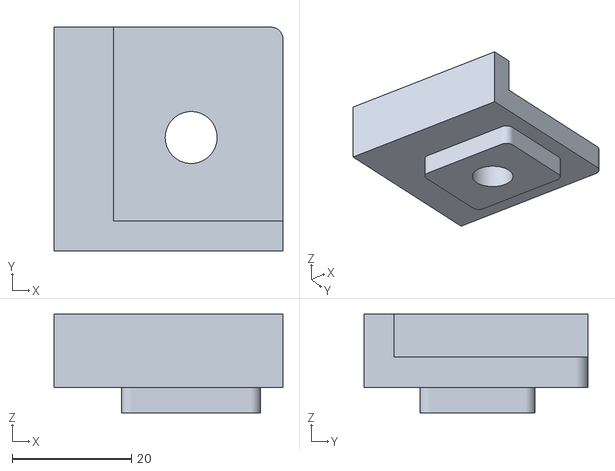
[picture p133: CAD file, 2026-10-06]
desk-dock/D7/print-review/height_shim_pack/plate.stl
38.4 x 37.5 x 16.6
