thereprocase/5680-dock/desk-dock/D7/print-review/plug_cap_quarter_turn_keeper/plate.stl

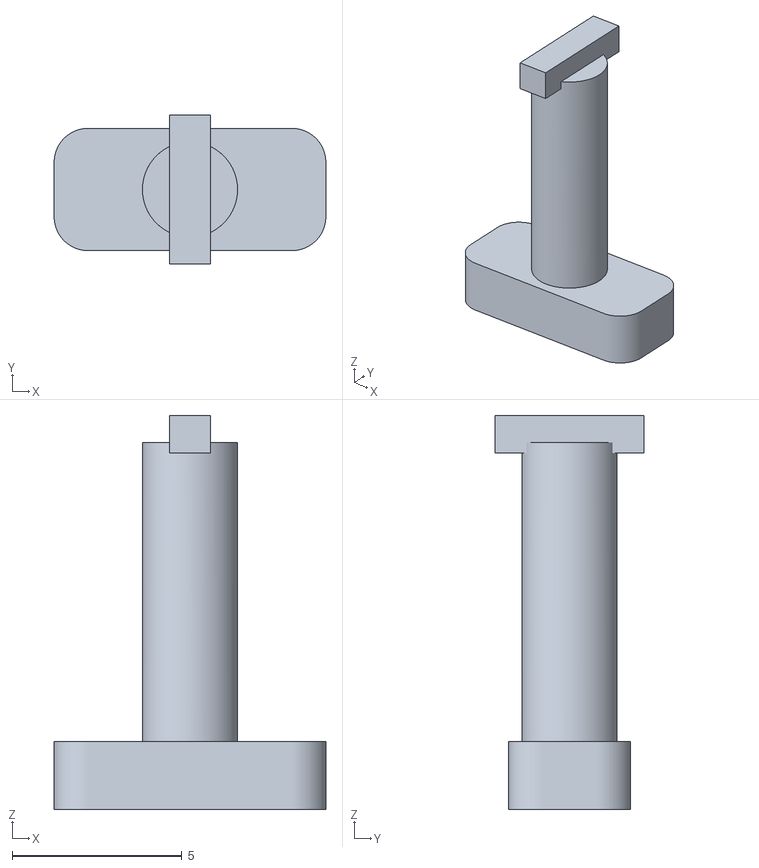
[picture p134: CAD file, 2026-10-06]
desk-dock/D7/print-review/plug_cap_quarter_turn_keeper/plate.stl
8.00 x 4.40 x 11.6
