thereprocase/5680-dock/desk-dock/D7/print-review/readiness/05_left_fan_cap/plate.stl

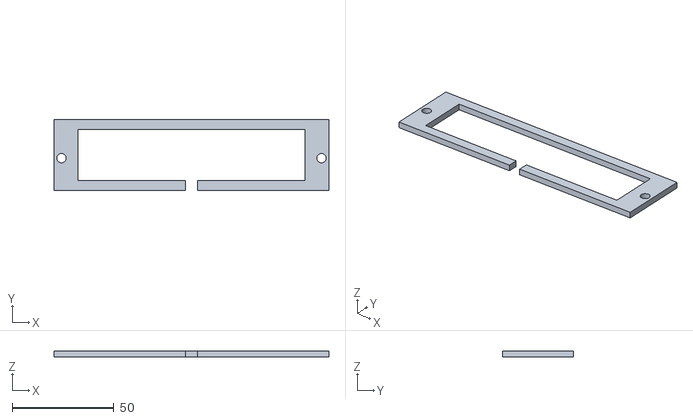
[picture p135: CAD file, 2026-10-06]
desk-dock/D7/print-review/readiness/05_left_fan_cap/plate.stl
135.4 x 35.1 x 3.00
