thereprocase/5680-dock/desk-dock/D7/print-review/sliding_plug_cap/plate.stl

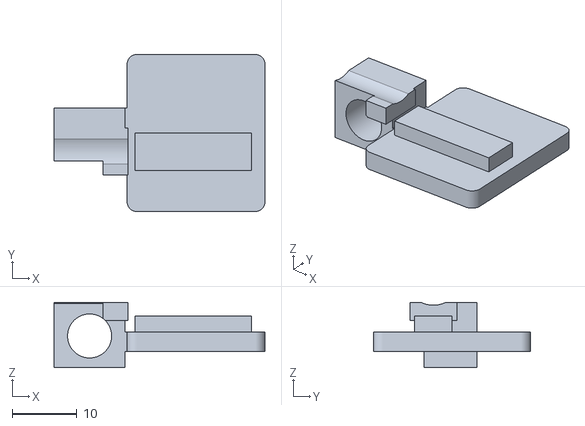
[picture p136: CAD file, 2026-10-06]
desk-dock/D7/print-review/sliding_plug_cap/plate.stl
32.6 x 24.3 x 10.1
