thereprocase/5680-dock/desk-dock/D7/print-review/stop_soft_tip/plate.stl

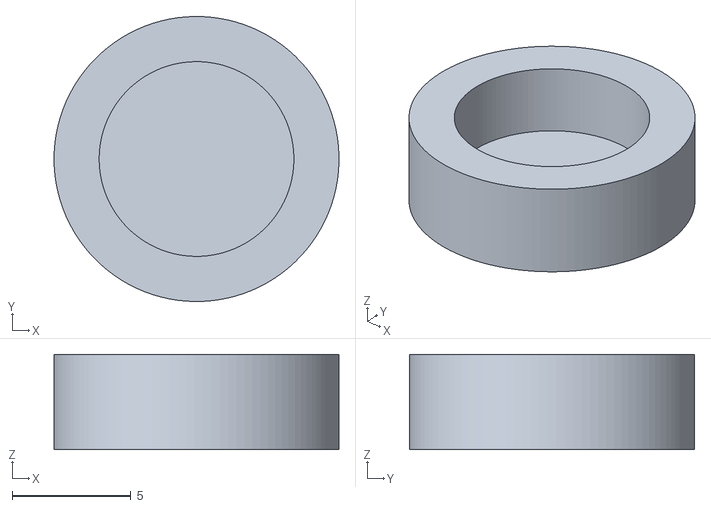
[picture p137: CAD file, 2026-10-06]
desk-dock/D7/print-review/stop_soft_tip/plate.stl
12.0 x 12.0 x 4.00
