thereprocase/5680-dock/desk-dock/D7/print-review/stop_thumb_knob/plate.stl

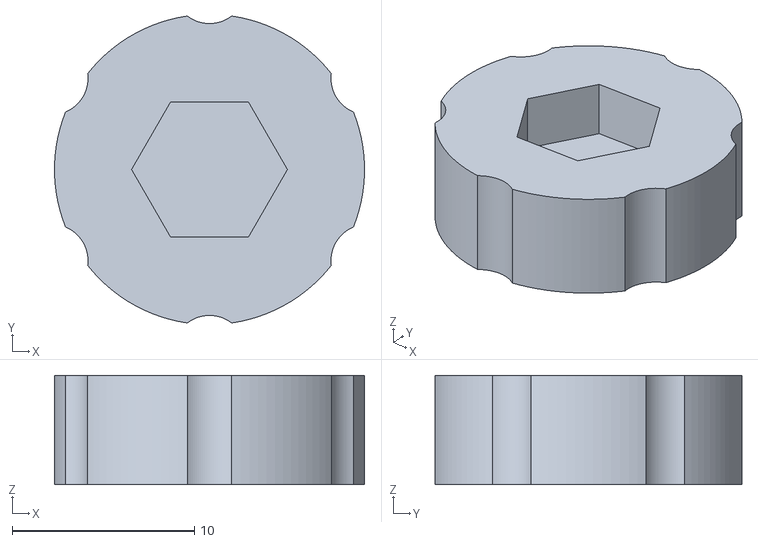
[picture p138: CAD file, 2026-10-06]
desk-dock/D7/print-review/stop_thumb_knob/plate.stl
17.0 x 16.8 x 6.00
