thereprocase/5680-dock/desk-dock/D7/print-review/X_depth_overmold_clamp/plate.stl

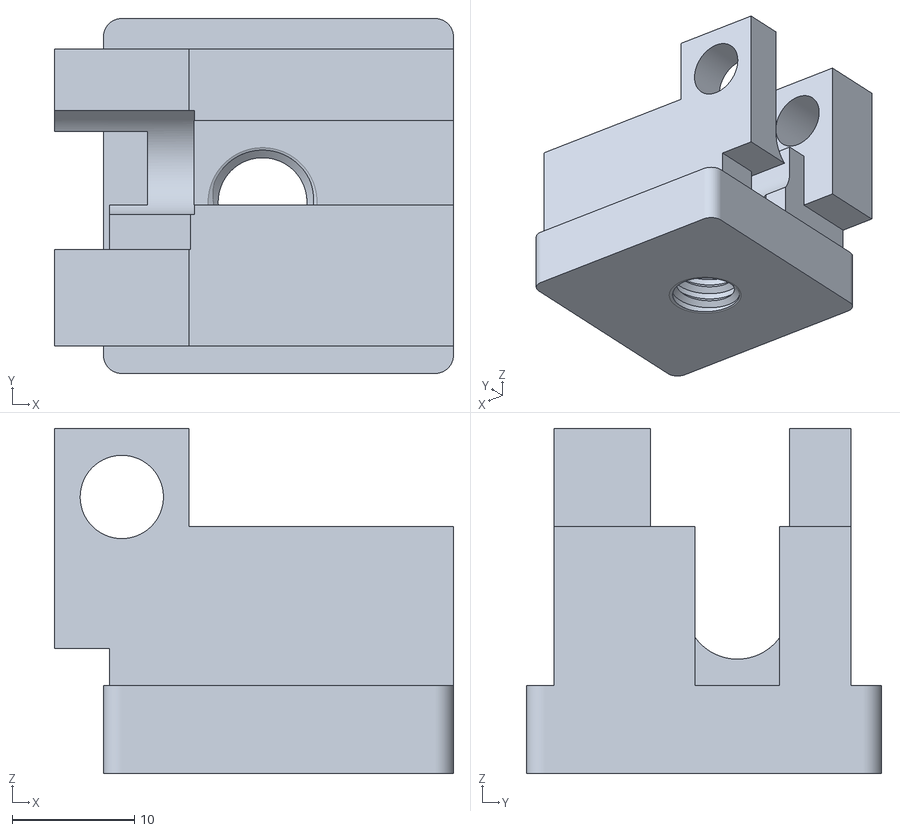
[picture p139: CAD file, 2026-10-06]
desk-dock/D7/print-review/X_depth_overmold_clamp/plate.stl
32.6 x 29.0 x 28.2
