thereprocase/5680-dock/desk-dock/D8/print/02_bottom_thumb_lock_2.stl

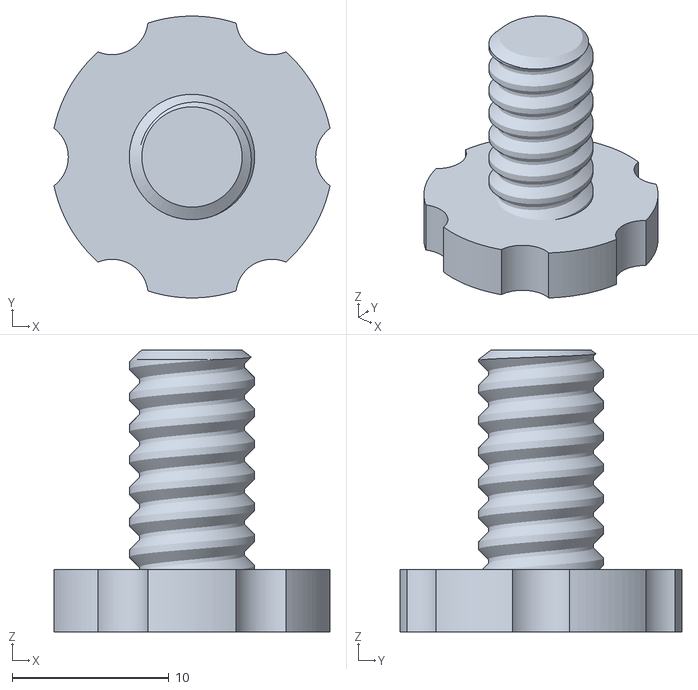
[picture p140: CAD file, 2026-10-06]
desk-dock/D8/print/02_bottom_thumb_lock_2.stl
17.6 x 18.0 x 18.0
