thereprocase/5680-dock/desk-dock/D8/quick-fit/D8-quick-fit-bracket.step

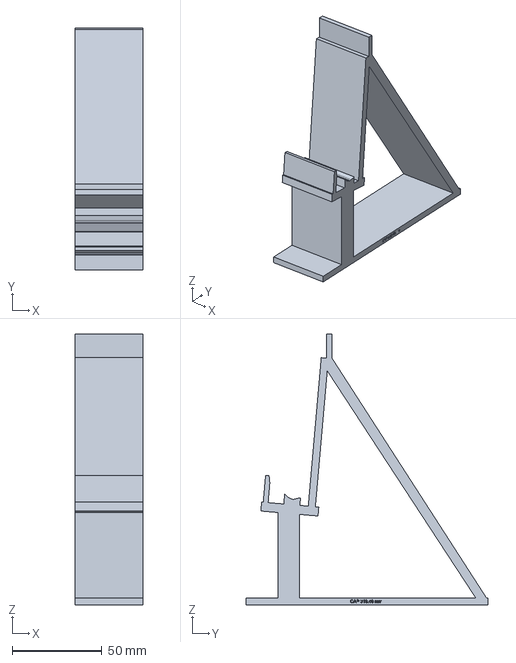
[picture p141: CAD file, 2026-10-06]
desk-dock/D8/quick-fit/D8-quick-fit-bracket.step
38.1 x 135.0 x 150.9 mm
