thereprocase/5680-dock/desk-dock/D8/quick-fit/R4/D8-R4-B-quick-fit-bracket-print-TWO.stl

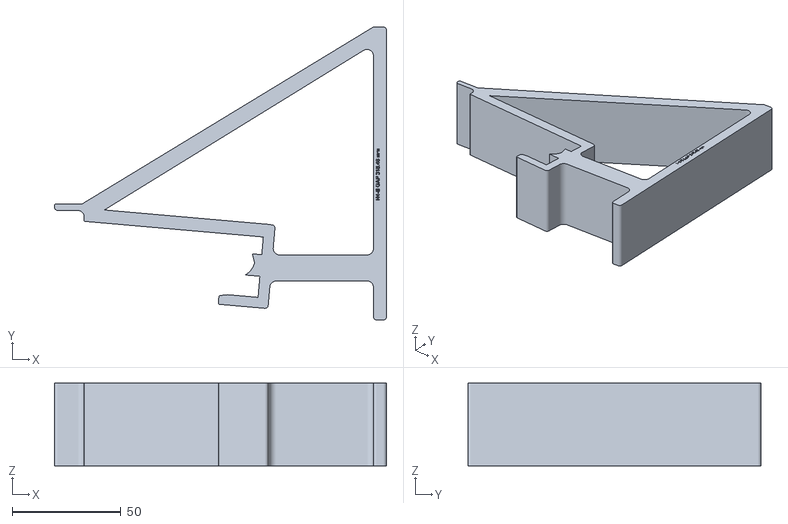
[picture p142: CAD file, 2026-10-06]
desk-dock/D8/quick-fit/R4/D8-R4-B-quick-fit-bracket-print-TWO.stl
152.9 x 135.0 x 38.1
