thereprocase/5680-dock/desk-dock/D8/quick-fit/R5/D8-R5-C-d9-source-quick-fit-bracket-print-TWO.stl

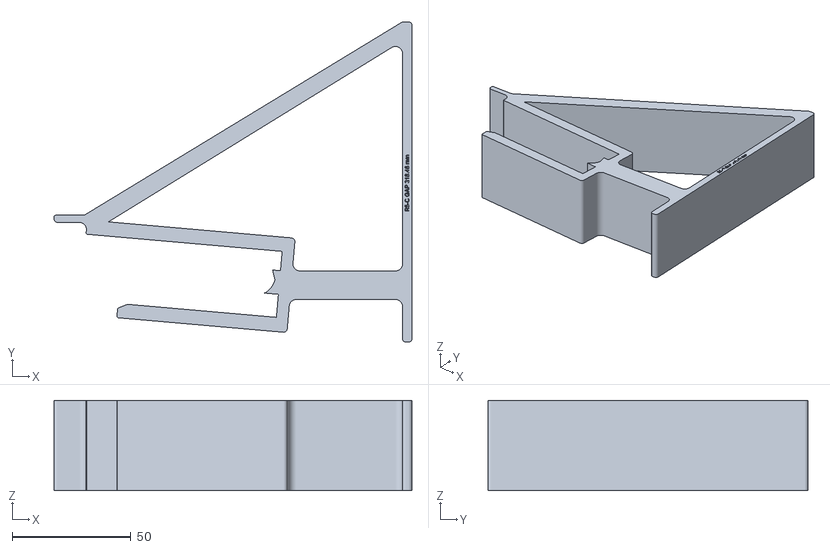
[picture p143: CAD file, 2026-10-06]
desk-dock/D8/quick-fit/R5/D8-R5-C-d9-source-quick-fit-bracket-print-TWO.stl
150.9 x 135.0 x 38.1
