thereprocase/5680-dock/desk-dock/D8/quick-fit/R6/D8-R6-seat-block-d9-source.step

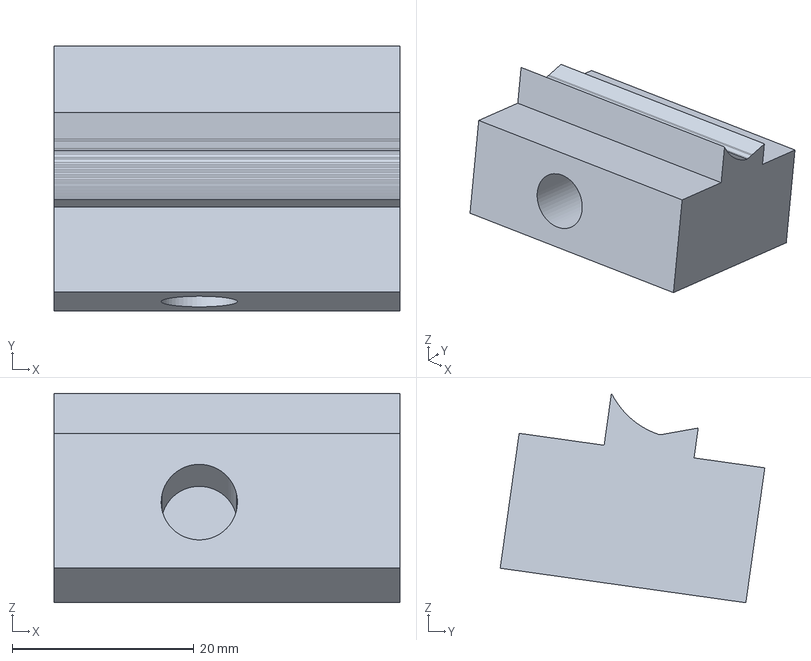
[picture p144: CAD file, 2026-10-06]
desk-dock/D8/quick-fit/R6/D8-R6-seat-block-d9-source.step
38.1 x 29.1 x 23.1 mm
