thereprocase/5680-dock/desk-dock/D8/quick-fit/R7/D8-R7-seat-peg-demo-T11.step

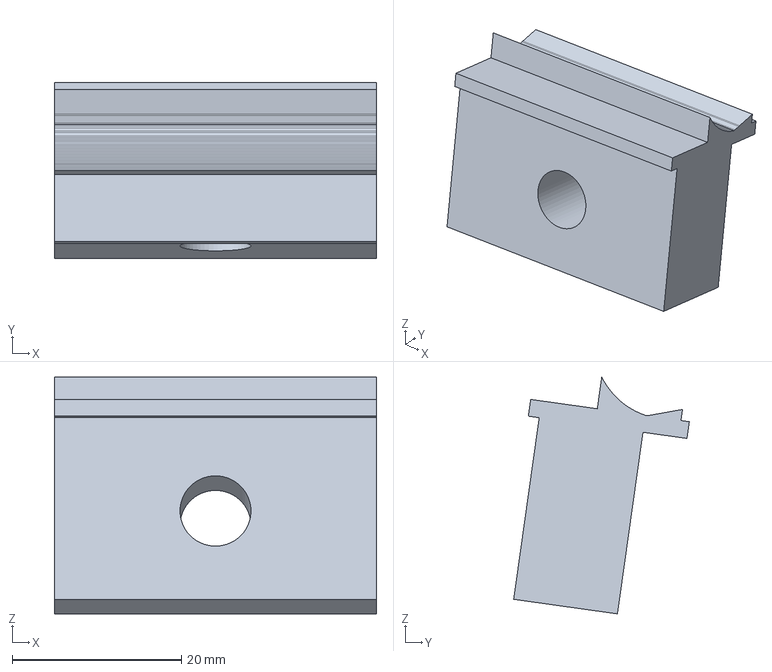
[picture p145: CAD file, 2026-10-06]
desk-dock/D8/quick-fit/R7/D8-R7-seat-peg-demo-T11.step
38.1 x 20.8 x 28.0 mm
