thereprocase/5680-dock/desk-dock/D9-P5/source-inputs/quick-fit/R7/D8-R7-socket-void-d9-source.step

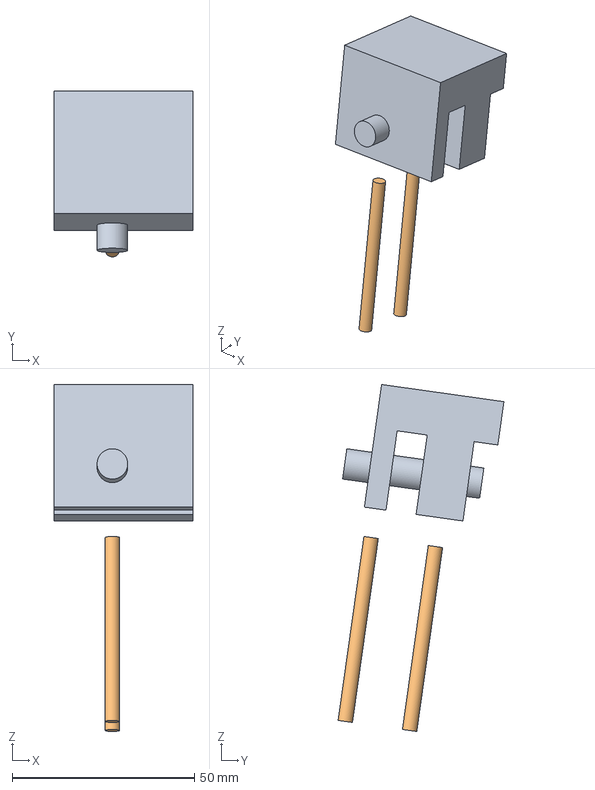
[picture p147: CAD file, 2026-10-06]
desk-dock/D9-P5/source-inputs/quick-fit/R7/D8-R7-socket-void-d9-source.step
38.1 x 45.5 x 95.3 mm
