thereprocase/5680-dock/desk-dock/Desk_Dock_CONCEPT.step

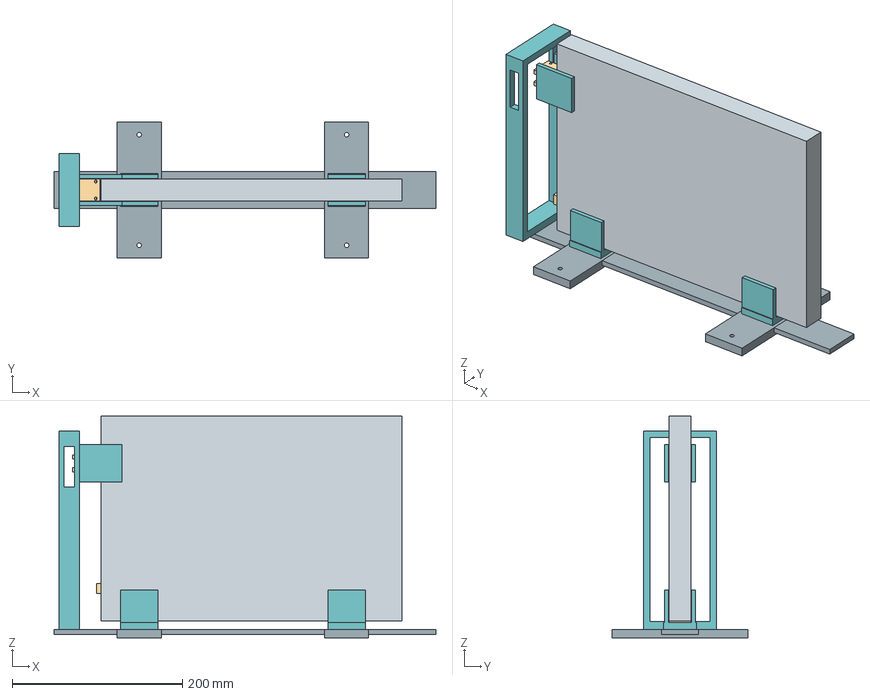
[picture p148: CAD file, 2026-10-06]
desk-dock/Desk_Dock_CONCEPT.step
448.7 x 160.0 x 260.3 mm
Metal_spine_envelope
Foot_1
Trough_saddle_1
Contact_pad_1
Foot_2
Trough_saddle_2
Contact_pad_2
Slotted_connector_frame
Cassette_lower_envelope
Cassette_upper_envelope
Dell_overmold_PLACEHOLDER
USB_C_tip_PLACEHOLDER
Port_level_guide_-18.485
Port_level_guide_13.485000000000001
Chassis_stop_ENVELOPE
Laptop_REFERENCE
