thereprocase/5680-dock/desk-dock/history/wide-d6/Precision_5680_D6.step

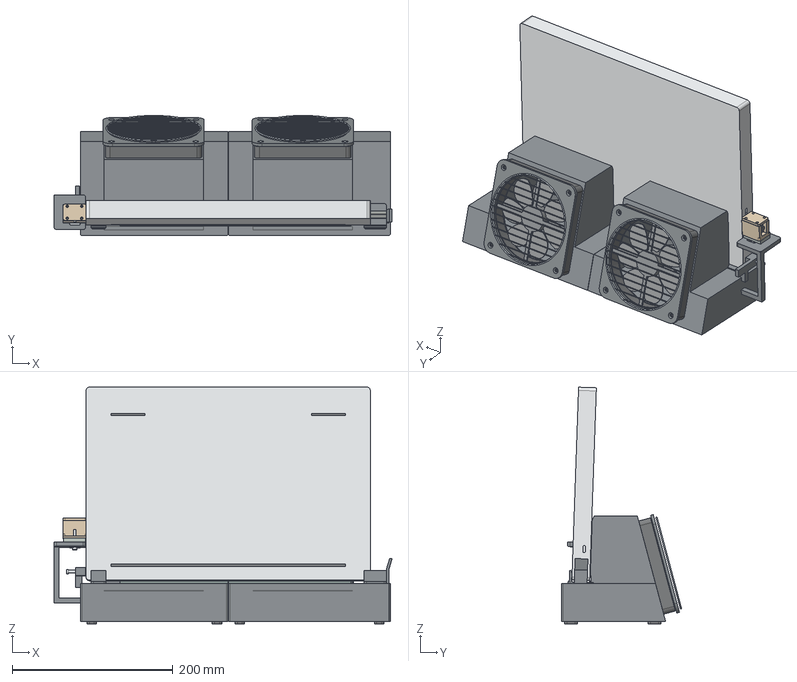
[picture p149: CAD file, 2026-10-06]
desk-dock/history/wide-d6/Precision_5680_D6.step
420.7 x 149.4 x 294.6 mm
01_foot_1.0_-20
01_foot_1.0_84
01_foot_156.8_-20
01_foot_156.8_84
01_120x15_fan_frame
01_fan_hub_struts
01_blade_0
01_blade_1
01_blade_2
01_blade_3
01_blade_4
01_blade_5
01_blade_6
01_outlet_guard
01_rounded_fan_bezel
02_foot_185.1_-20
02_foot_185.1_84
02_foot_358.7_-20
02_foot_358.7_84
02_120x15_fan_frame
02_fan_hub_struts
02_blade_0
02_blade_1
02_blade_2
02_blade_3
02_blade_4
02_blade_5
02_blade_6
02_outlet_guard
02_rounded_fan_bezel
corner_pad_far
corner_pad_near
lid_bearing_liner_1
lid_bearing_liner_2
hinge_seal_42.0_-12.3
hinge_seal_177.3_-12.3
hinge_seal_42.0_11.0
hinge_seal_177.3_11.0
height_shim_pack
X_depth_overmold_clamp
front_capture_clip_0p8mm_metal
removable_plug_cap
Dell_plug_overmold_REFERENCE
USB_C_shell_REFERENCE
cassette_lock_-8.0
cassette_washer_-8.0
cassette_lock_8.0
cassette_washer_8.0
independent_M4_stop
stop_soft_tip
Precision_5680_REFERENCE
RUBBER_FOOT_rear_strip
RUBBER_FOOT_front_left
RUBBER_FOOT_front_right
01_manifold_with_cradle
02_manifold_with_cradle
