thereprocase/5680-dock/docs/downloads/10_right_fan_tray.stl

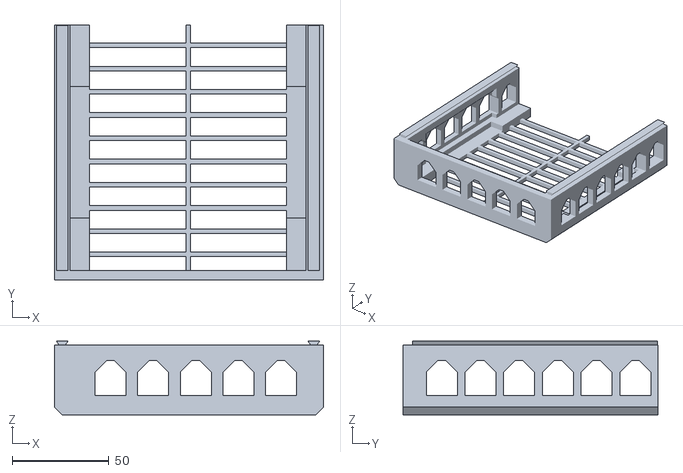
[picture p150: CAD file, 2026-10-06]
docs/downloads/10_right_fan_tray.stl
139.0 x 131.7 x 38.0
