thereprocase/5680-dock/docs/models/after/05_left_fan_retainer.stl

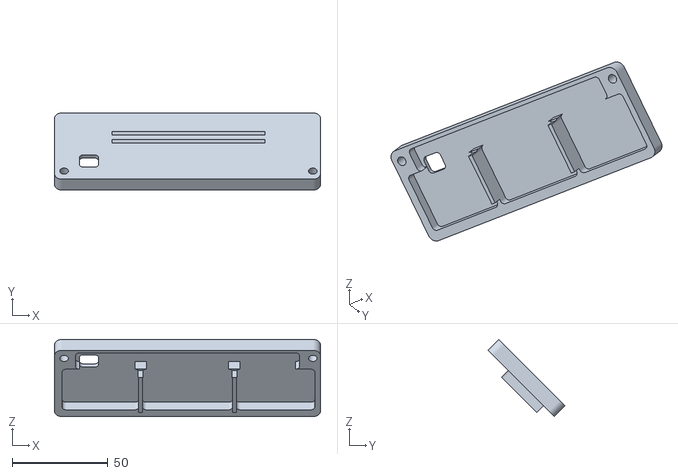
[picture p151: CAD file, 2026-10-06]
docs/models/after/05_left_fan_retainer.stl
139.0 x 40.3 x 40.3
