thereprocase/5680-dock/docs/models/before/10_right_fan_tray.stl

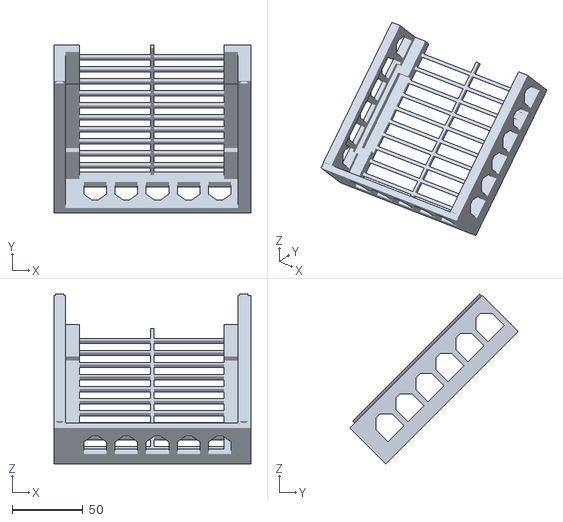
[picture p152: CAD file, 2026-10-06]
docs/models/before/10_right_fan_tray.stl
139.0 x 118.8 x 119.9
