thereprocase/5680-dock/docs/models/minimalist/13-inch-example/10_right_fan_key.stl

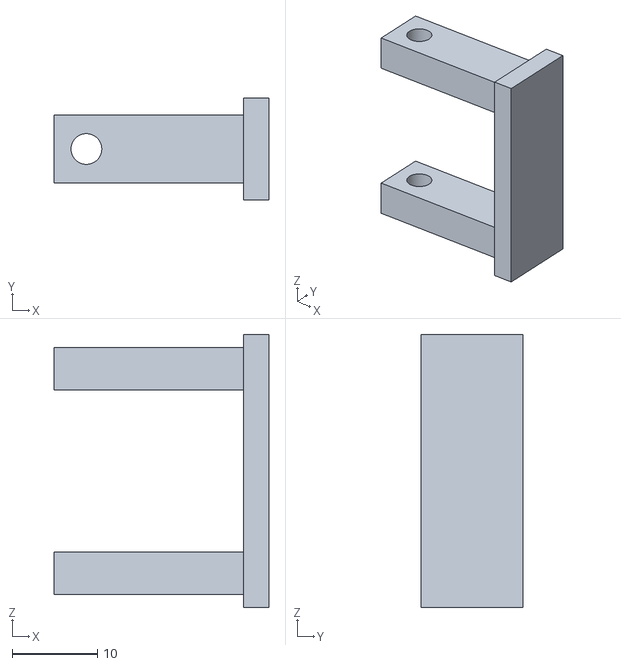
[picture p153: CAD file, 2026-10-06]
docs/models/minimalist/13-inch-example/10_right_fan_key.stl
25.2 x 12.0 x 32.0
