thereprocase/5680-dock/docs/models/minimalist/17-inch-example/20_right_cap_pin_2.stl

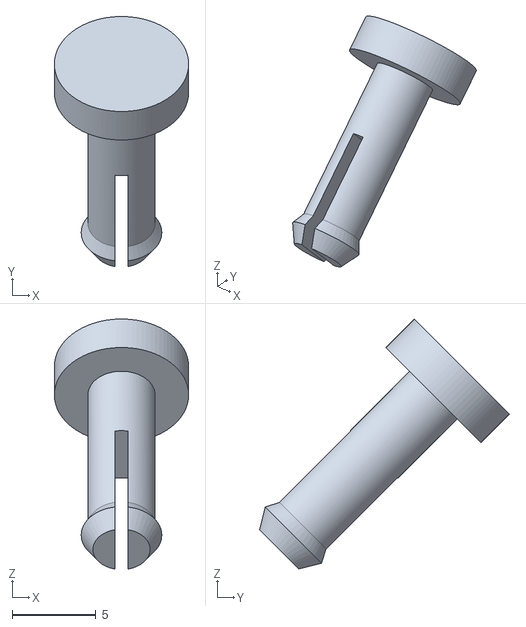
[picture p154: CAD file, 2026-10-06]
docs/models/minimalist/17-inch-example/20_right_cap_pin_2.stl
8.00 x 14.9 x 14.9
