thereprocase/5680-dock/docs/printables/d9-p1/04-M2-outer-cradle.3mf

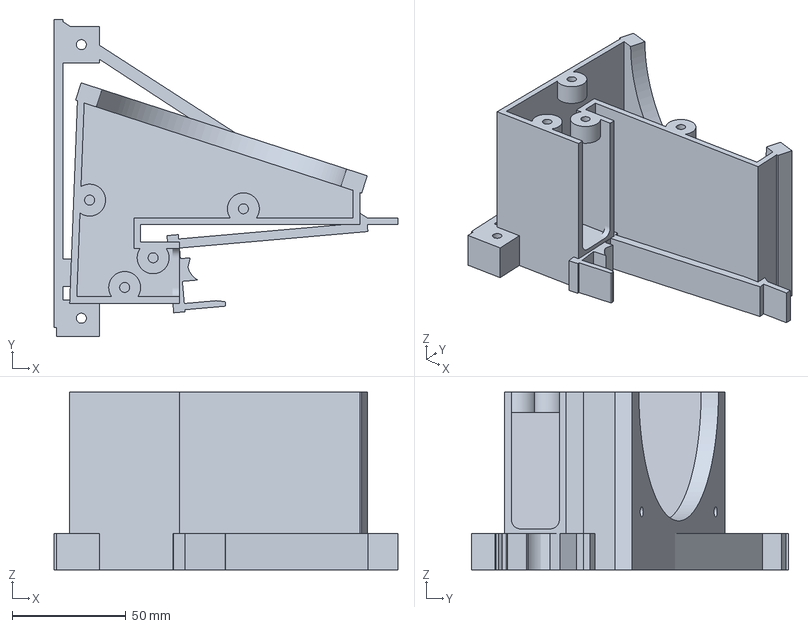
[picture p155: CAD file, 2026-10-06]
docs/printables/d9-p1/04-M2-outer-cradle.3mf
150.9 x 139.0 x 78.0 mm
