thereprocase/5680-dock/docs/printables/d9-p2/00-START-HERE-fastener-fit.3mf

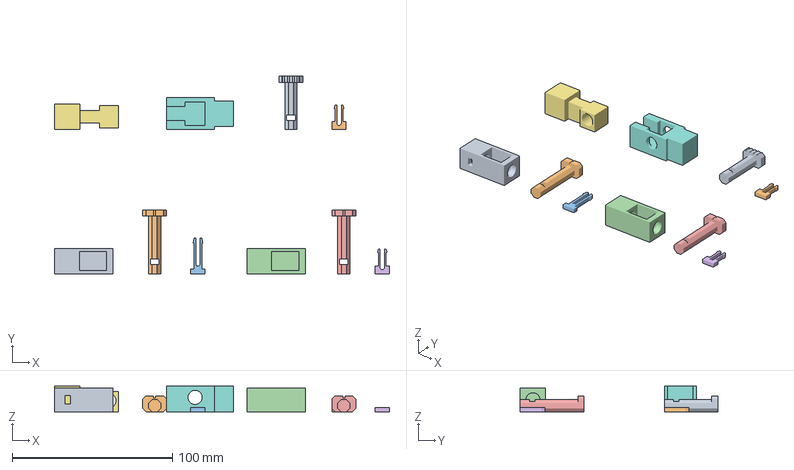
[picture p156: CAD file, 2026-10-06]
docs/printables/d9-p2/00-START-HERE-fastener-fit.3mf
209.0 x 123.4 x 16.0 mm
fan-socket-fit-fixture
M1-fan-3-pin
M1-fan-3-key
side-socket-fit-fixture
M1-fan-1-pin
M1-fan-1-key
T-joint-fit-L
T-joint-fit-R
front-lap-pin
front-lap-key
