thereprocase/5680-dock/docs/printables/d9-p3/06-M2-guard-rear-ties.3mf

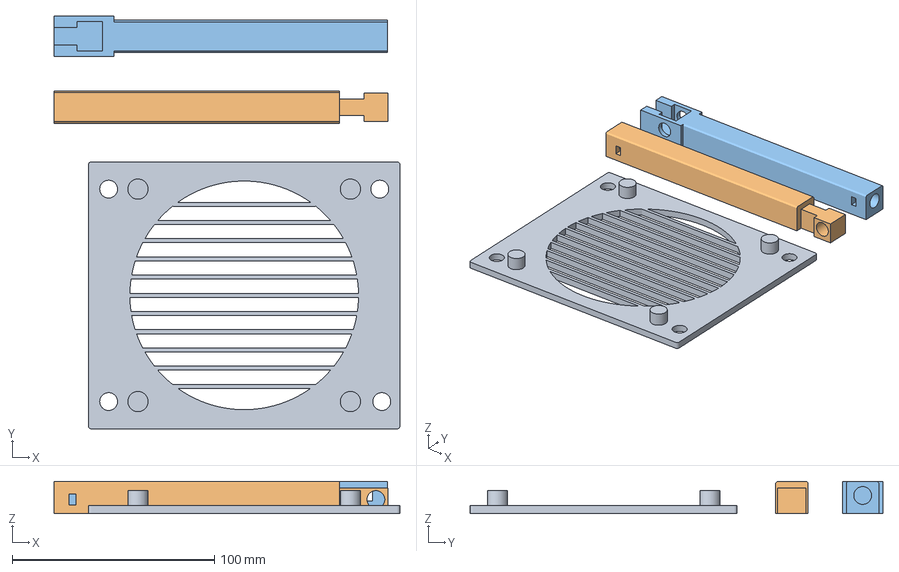
[picture p157: CAD file, 2026-10-06]
docs/printables/d9-p3/06-M2-guard-rear-ties.3mf
171.0 x 204.0 x 16.0 mm
M2-fan-guard
rear-tie-L
rear-tie-R
