thereprocase/5680-dock/docs/printables/d9-p4/02-M1-inner.3mf

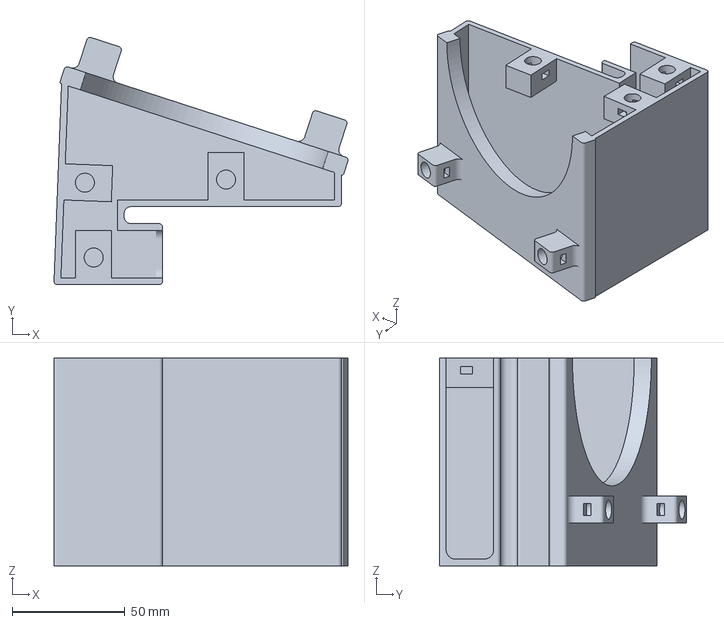
[picture p158: CAD file, 2026-10-06]
docs/printables/d9-p4/02-M1-inner.3mf
130.1 x 109.4 x 91.8 mm
