thereprocase/5680-dock/docs/printables/d9-p5/10-gap-trim.3mf

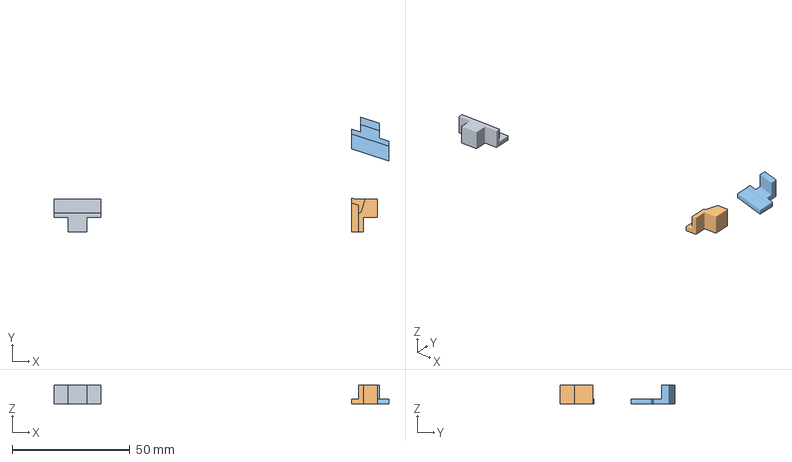
[picture p159: CAD file, 2026-10-06]
docs/printables/d9-p5/10-gap-trim.3mf
142.0 x 48.6 x 8.00 mm
align-aid-front
align-aid-top
align-aid-fan
