thereprocase/5680-dock/docs/printables/fit-v5/Precision_5680_V5_Rail_Plus_3p5mm_Fit_Coupons.3mf

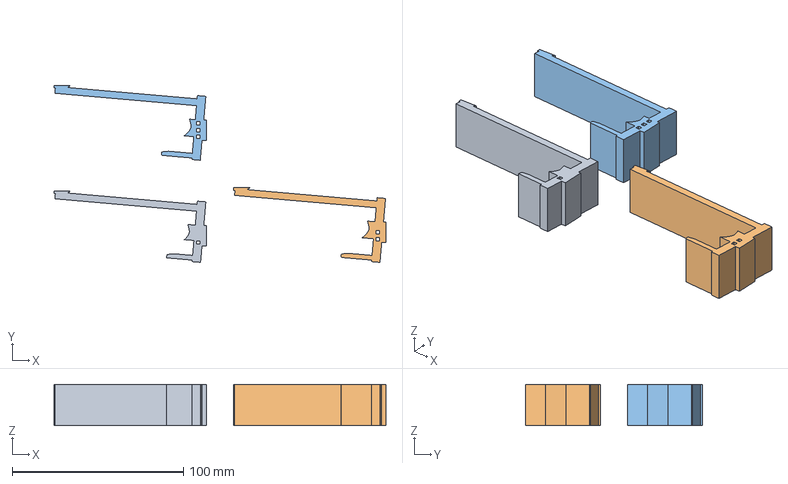
[picture p160: CAD file, 2026-10-06]
docs/printables/fit-v5/Precision_5680_V5_Rail_Plus_3p5mm_Fit_Coupons.3mf
193.8 x 103.2 x 24.0 mm
A_R1_full_rail_plus_3p5mm_X_to_print_Z
B_R2_full_rail_plus_3p5mm_X_to_print_Z
C_R2_full_rail_plus_3p5mm_plus_1mm_seat_relief_X_to_print_Z
