thereprocase/5680-dock/docs/printables/r4-fit-pair/Precision_5680_R4C_Bracket_Pair_plus_P2_Fit.3mf

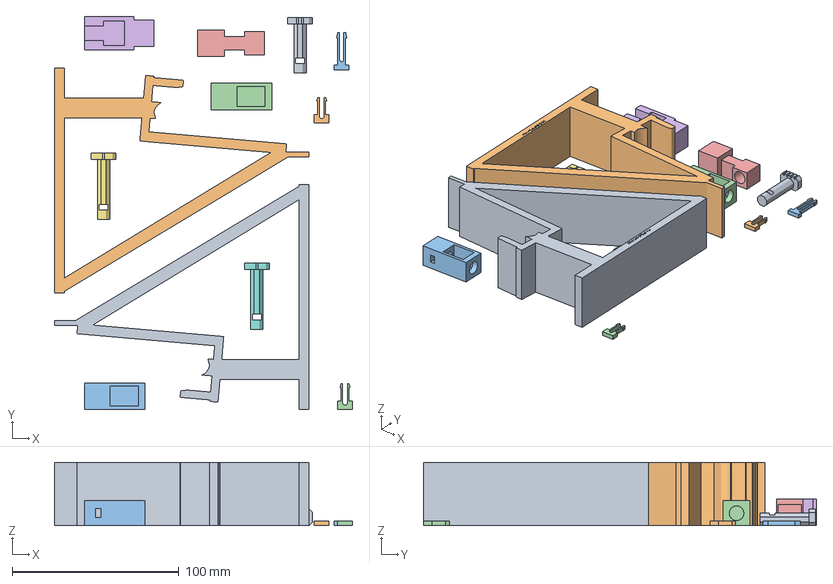
[picture p161: CAD file, 2026-10-06]
docs/printables/r4-fit-pair/Precision_5680_R4C_Bracket_Pair_plus_P2_Fit.3mf
179.0 x 236.0 x 38.1 mm
D8-R4-C-quick-fit-bracket-print-TWO
D8-R4-C-quick-fit-bracket-print-TWO-2
fan-socket-fit-fixture
side-socket-fit-fixture
T-joint-fit-L
T-joint-fit-R
M1-fan-1-pin
M1-fan-3-pin
front-lap-pin
M1-fan-1-key
M1-fan-3-key
front-lap-key
