thereprocase/5680-dock/freecad/print_refinements_oriented/03_left_fan_duct.stl

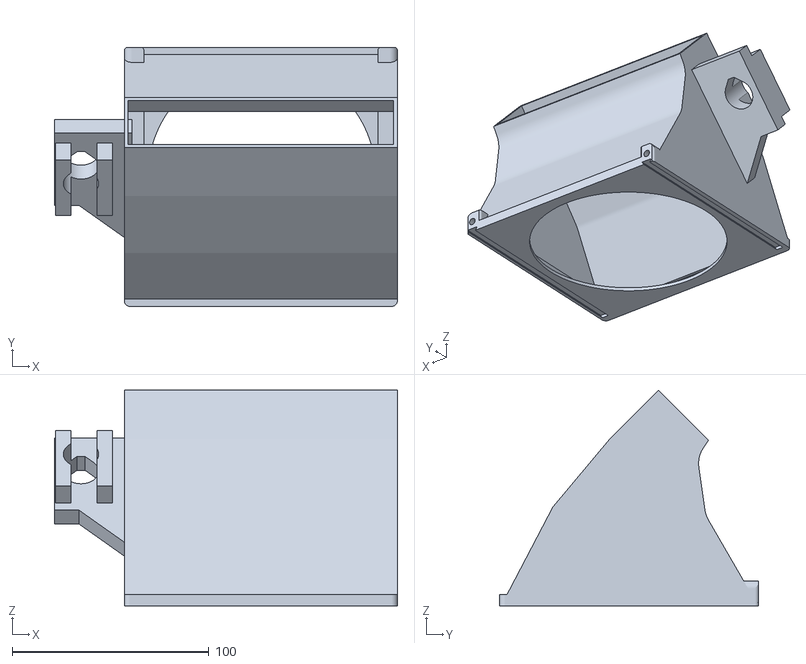
[picture p164: CAD file, 2026-10-06]
freecad/print_refinements_oriented/03_left_fan_duct.stl
174.5 x 131.7 x 109.6
