thereprocase/5680-dock/fusion/cfd/cases/OpenCFD_v2412/installed_pressure10_v3/constant/triSurface/fluid_boundary.stl

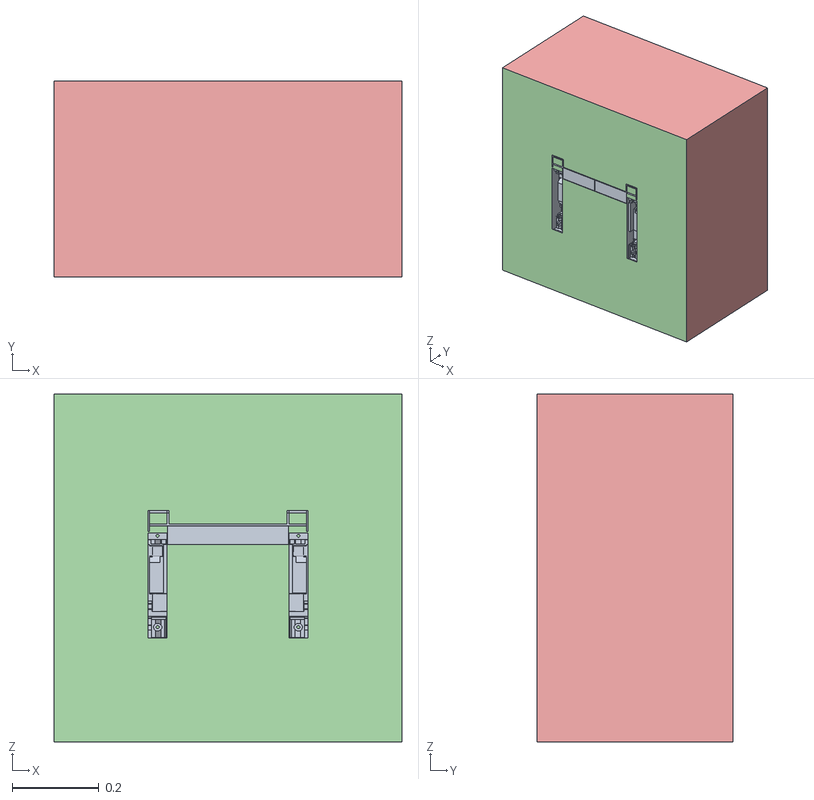
[picture p165: CAD file, 2026-10-06]
fusion/cfd/cases/OpenCFD_v2412/installed_pressure10_v3/constant/triSurface/fluid_boundary.stl
0.8 x 0.45 x 0.8
printed
laptop
noctua
wall_plane
ambient_openings
