thereprocase/5680-dock/fusion/cfd/geometry/fluid.step

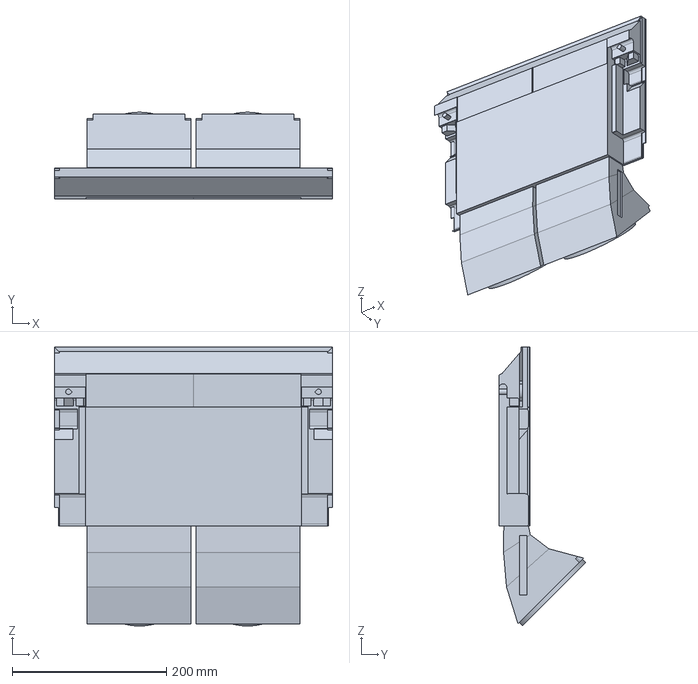
[picture p167: CAD file, 2026-10-06]
fusion/cfd/geometry/fluid.step
360.0 x 112.3 x 361.3 mm
