thereprocase/5680-dock/fusion/cfd/geometry_gap8/outlet.stl

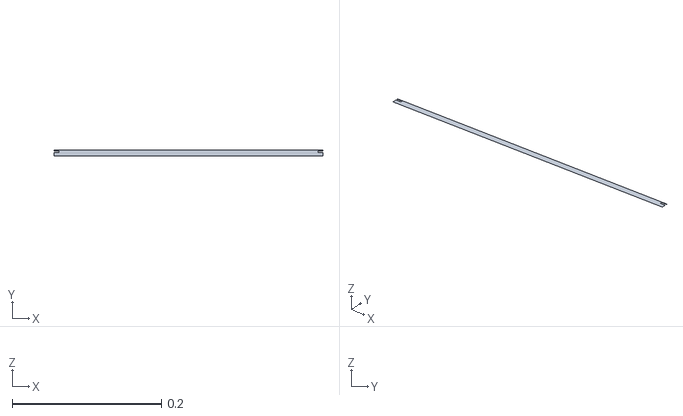
[picture p169: CAD file, 2026-10-06]
fusion/cfd/geometry_gap8/outlet.stl
0.36 x 0.008 x 0
