thereprocase/5680-dock/fusion/cfd/geometry_installed/printed.stl

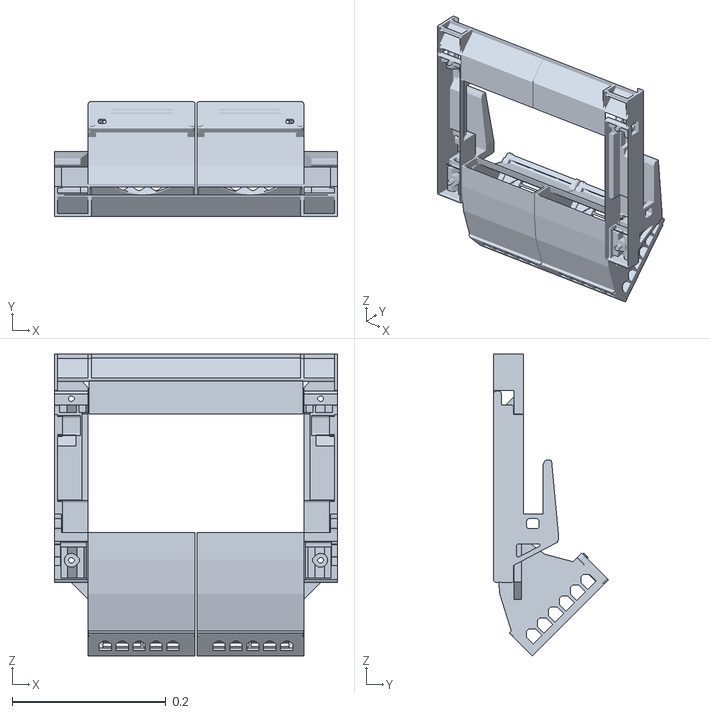
[picture p170: CAD file, 2026-10-06]
fusion/cfd/geometry_installed/printed.stl
0.368 x 0.149 x 0.392
