thereprocase/5680-dock/fusion/cfd/geometry_revh/laptop.stl

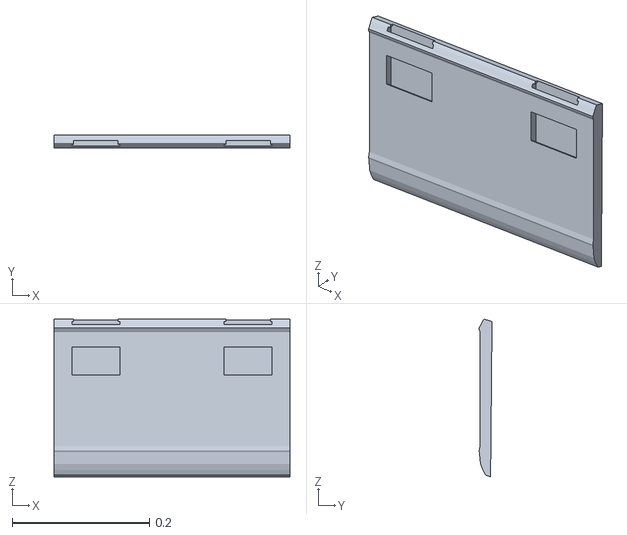
[picture p172: CAD file, 2026-10-06]
fusion/cfd/geometry_revh/laptop.stl
0.344 x 0.0191 x 0.23
