thereprocase/5680-dock/fusion/cfd/geometry_traced_v1/zones/noctua_fan_left.stl

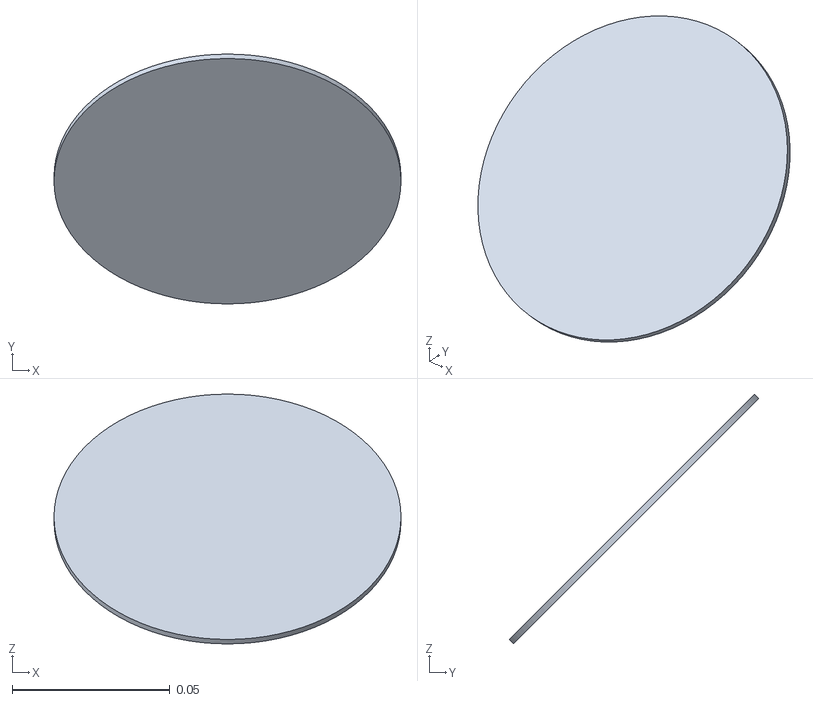
[picture p174: CAD file, 2026-10-06]
fusion/cfd/geometry_traced_v1/zones/noctua_fan_left.stl
0.11 x 0.0792 x 0.0792
