thereprocase/5680-dock/fusion/output/Fusion_native_pin.step

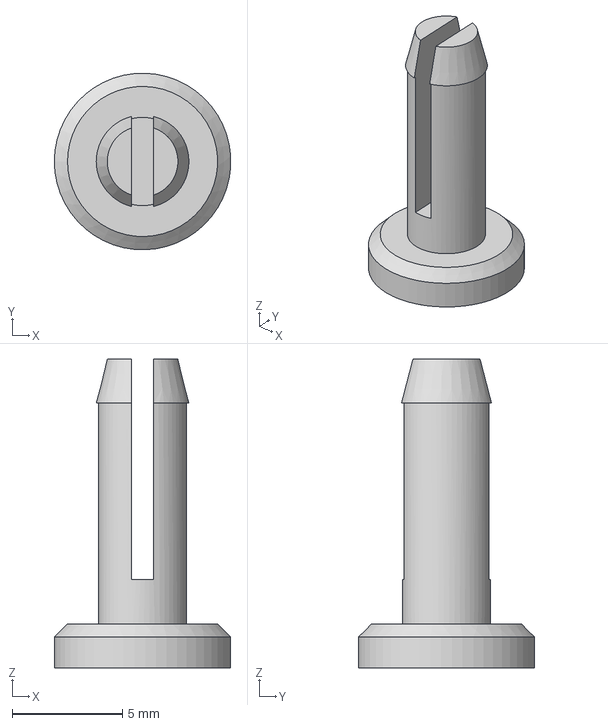
[picture p175: CAD file, 2026-10-06]
fusion/output/Fusion_native_pin.step
7.99 x 8.00 x 14.0 mm
