thereprocase/5680-dock/minimalist/presets/14-inch-example/print/17_left_cap_pin_1.step

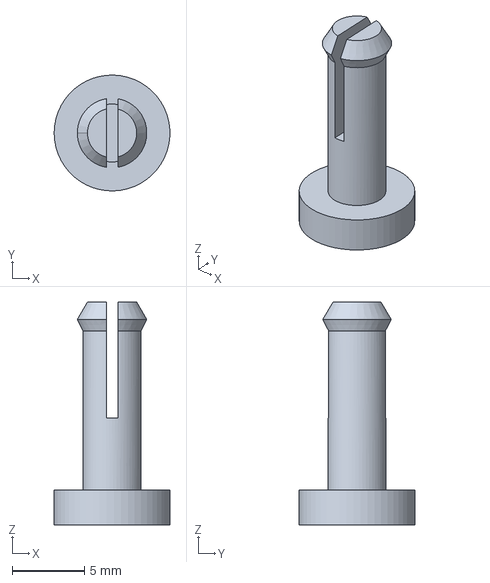
[picture p176: CAD file, 2026-10-06]
minimalist/presets/14-inch-example/print/17_left_cap_pin_1.step
7.99 x 8.00 x 15.4 mm
