thereprocase/5680-dock/minimalist/presets/15-6-inch-example/print/03_left_fan_cage.step

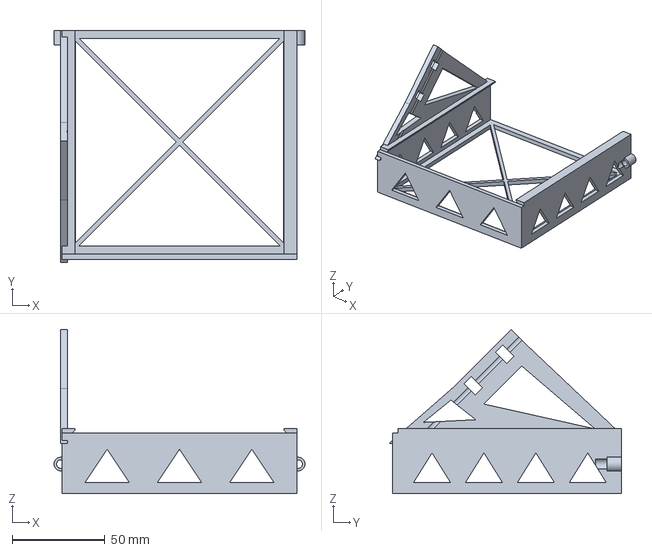
[picture p177: CAD file, 2026-10-06]
minimalist/presets/15-6-inch-example/print/03_left_fan_cage.step
135.4 x 125.4 x 88.7 mm
