thereprocase/5680-dock/outlet_gap_variants/left_outlet_rail_gap_16mm.step

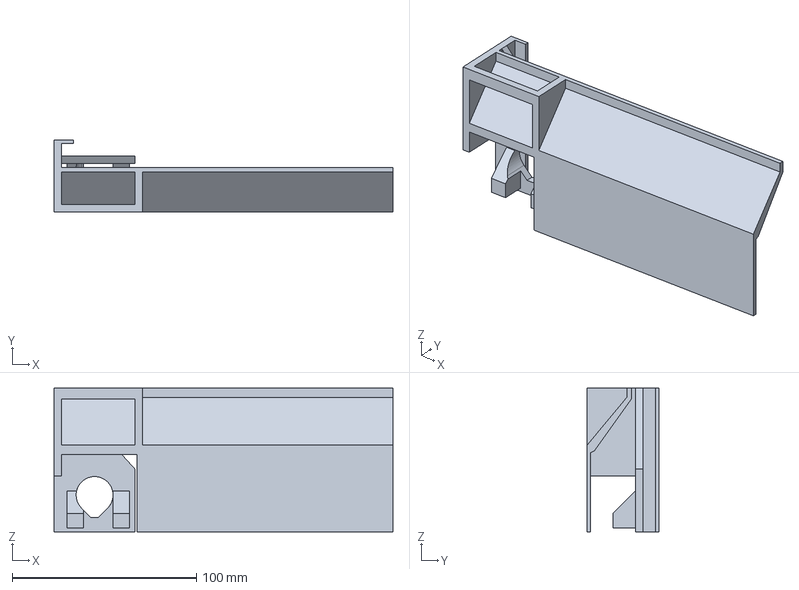
[picture p178: CAD file, 2026-10-06]
outlet_gap_variants/left_outlet_rail_gap_16mm.step
183.8 x 39.0 x 78.0 mm
