thereprocase/5680-dock/print_ready/08_right_outlet_rail.3mf

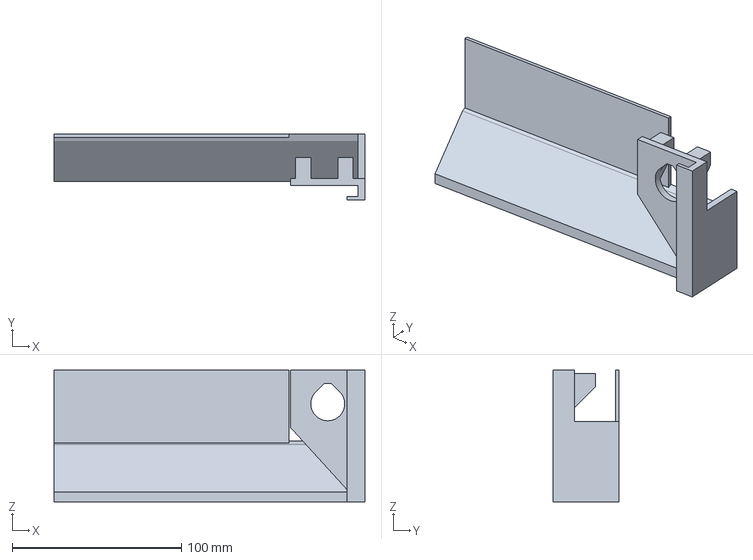
[picture p179: CAD file, 2026-10-06]
print_ready/08_right_outlet_rail.3mf
183.8 x 39.0 x 78.0 mm
