thereprocase/5680-dock/desk-dock/D8/print/cassette_Z_saddle.stl

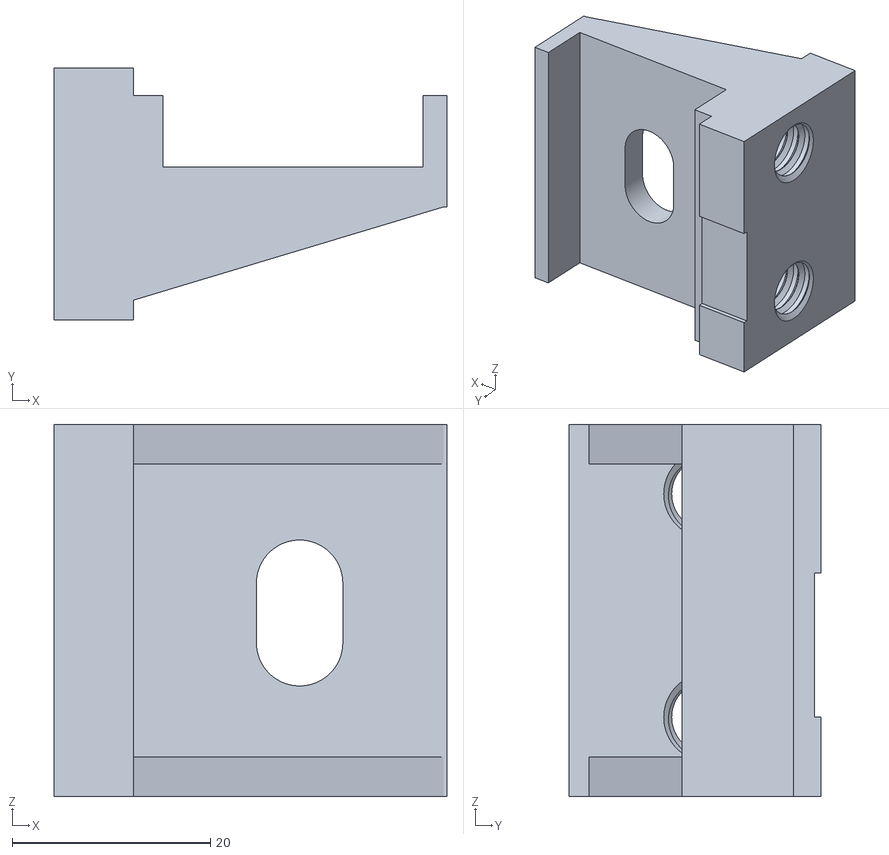
[picture p181: CAD file, 2026-10-06]
desk-dock/D8/print/cassette_Z_saddle.stl
39.6 x 25.4 x 37.5
