thereprocase/5680-dock/desk-dock/D8/quick-fit/R7/D8-R7-fence-peg-plug-demo-T44.step

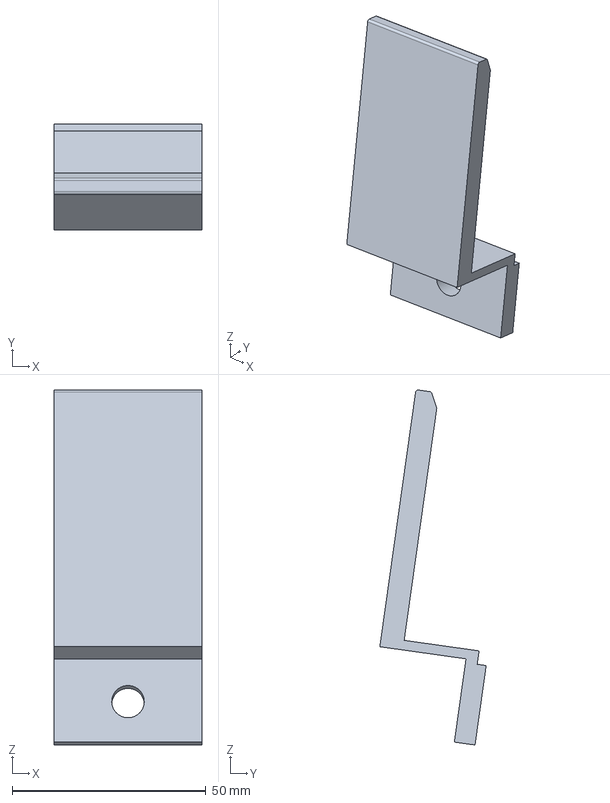
[picture p182: CAD file, 2026-10-06]
desk-dock/D8/quick-fit/R7/D8-R7-fence-peg-plug-demo-T44.step
38.1 x 27.5 x 91.6 mm
