thereprocase/5680-dock/desk-dock/D9-P5/source-inputs/quick-fit/R7/D8-R7-frame-d9-source.step

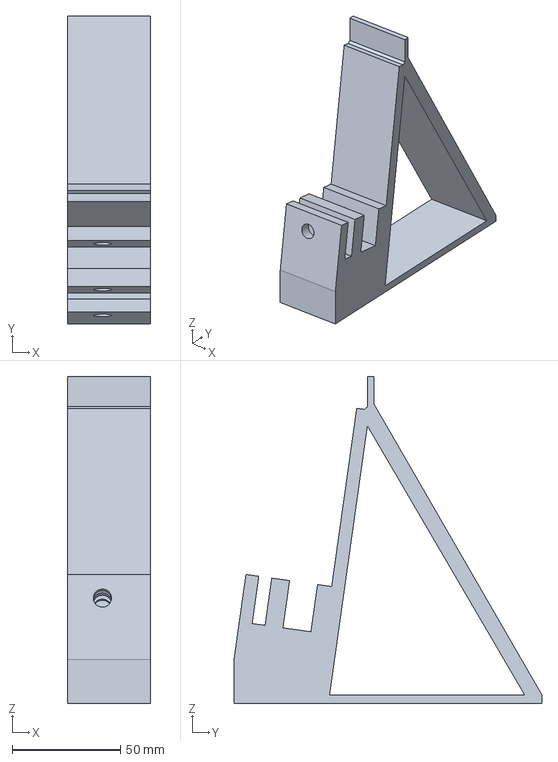
[picture p183: CAD file, 2026-10-06]
desk-dock/D9-P5/source-inputs/quick-fit/R7/D8-R7-frame-d9-source.step
38.1 x 142.0 x 150.9 mm
