thereprocase/5680-dock/docs/printables/d9-p3/README.md

# Precision 5680 D9 P3: R4-C cradle contact and finished edges

P3 is the D9 P2 no-metal-hardware dock with two changes and nothing else:

1. **Cradle contact from the R4-C profile.** The printed V5 coupon C seated
   (R2 seat with the 1-mm local relief) once the lid rail was moved 3.5 mm
   outward, so both outer cradles now carry that seat and that rail position,
   with the rail 6 mm thick and the short fence 2 mm thicker on its outer face.
   The cradle base stays 4 mm so every foot remains coplanar with the ties.
2. **Printable edge treatment.** Profile corners that run along each part's
   print Z are filleted (3 mm concave for stress relief, 1.5 mm convex for
   looks); the ties' top edges carry a 0.8-mm chamfer; bed edges are untouched.
   Every mating zone is protected and unchanged: air cavities, fan seats,
   blind sockets, pin bores, key slots, T joints, guard bars and standoffs,
   and the laptop contact band. Pins, keys and the fit fixtures are
   byte-identical to P2, so the printed P2 fit plate remains the valid trial.

Connections, plenum geometry, fan pose, guards and braces are P2. Two purchased
120 x 120 x 25 mm fans are still required. The plug mechanism is excluded.

## What to print

The P2 fastener fit plate has already been printed together with the R4-C
bracket pair; there is no plate 00 in this kit. Print plates **01 through 07
once each** for one dock: ten major parts, 20 pins and 20 locking keys.
**OPEN-ME.3mf** is an identical copy of plate 01. Each numbered 3MF contains
one frozen, named plate with matching embedded G-code; matching standalone
G-code, oriented STL and assembly-coordinate STEP bodies are included. The
STL poses are intentional; do not auto-orient them. Print the two outer
cradle plates (01 and 04) only after the R4-C bracket pair has carried the
laptop; the other five plates do not depend on the contact geometry.

Printer/profile: Repro Bambu P1S, 0.4 mm nozzle, Generic PETG Starter,
textured PEI, 0.2 mm layers, five walls, six top/bottom layers, 5 mm brim,
40 % gyroid on the main plates and 100 % on the fasteners. Supports are
enabled for accessible hidden surfaces. Confirm the actual printer and
filament before using the saved G-code.

## Parts and identification

| Pin use | Quantity | Head-edge notches | Shaft length | Matching key |
| --- | ---: | ---: | ---: | --- |
| Fan guards | 8 | 1 | 36 mm | Six long; two short at the outboard lower sockets |
| Frame ends | 4 | 2 | 32.8 mm | Long |
| Plenum seams | 6 | 3 | 26 mm | Long |
| Brace T joints | 2 | 4 | 29.4 mm | Short |

There are 16 long keys (22.5 mm overall, 16 mm grip) and four short keys
(15.5 mm overall, 8 mm grip). Each pin has an additional 4 mm head. Part
names are retained in the Orca projects and CAD files.

## Assembly

1. Remove supports and brim while the shell halves are open. Clean pin bores
   and key windows without enlarging their bearing surfaces.
2. Join each front/rear brace on the bench: lower the male T tongue into the
   floor-backed female pocket, insert a four-notch pin, then its short key.
   The complete brace attaches to the cradle feet with two-notch pins and
   long keys.
3. Dry-fit each matching M1/M2 shell pair. Join its three internal tabs with
   three-notch pins and long keys before fitting the fans. The rear-wall seam
   key inserts downward through the open mouth. Optional thin seam sealant
   addresses physical leakage; it is not the structural connection.
4. Place each fan against its flange and add the guard. Four one-notch pins
   run outside the fan frame into blind sockets; factory screw holes are
   unused. The lower outboard sockets take short keys from the outer cradle
   side; rotate those pins a quarter-turn so the cross-slot faces that side.
5. To service a rear brace T joint, remove the complete brace from the cradle
   feet first. Remove fans before servicing the internal plenum retainers.

## Verification and limits

All 50 assembly solids are valid, single-component watertight meshes. No
nominal volume interference exists between assembly parts, purchased fan
envelopes or the upper laptop envelope. Pin/key insertion was re-checked at
five positions along each path with compressed key-barb geometry. Both
plenums pass the nominal enclosure checks with the two actual shell halves
and each named port capped in turn, and the edge treatment changed the
intended air volume of each module by exactly zero. Every plate passed the
native Orca verification: unchanged poses and placement, all roads inside the
usable bed and outside the exclusion zone, expected heights, matching
embedded and standalone G-code, and per-object support and bridge counts
recorded (hidden supports on shells, guards and ties are intended).

This is a prototype print kit. Physical seating of the R4-C cradles, pin/key
fit, support removal, loaded stability, creep, retention durability, cooling
and acoustics remain untested. No 800 RPM performance claim is made.

## Editable source and provenance

`source/build_d9.py` runs with CadQuery 2.8, trimesh, Shapely and Pillow, with
`source/dress.py` for the edge treatment. The frozen R4-C cradle source
(`source-inputs/quick-fit/R4`, built from the R2 bracket by the R4 builder with
`--variant C --base-thickness 4 --tag d9-source`), the R2 inputs and the
geometry JSON are included. STEP files preserve assembled coordinates; STL
files preserve print poses. Preparation helpers and frozen profiles are
included. SHA256.json and the ZIP payload are verified against the standalone
print directory.

## Orca estimates

- assembly plates 01 to 07: 1098.17 g; 46h 18m 28s.
- outer cradle plates 01 and 04: 430.07 g; 19h 44m 47s.
- contact independent plates 02 03 05 06 07: 668.10 g; 26h 33m 41s.
