thereprocase/5680-dock/docs/printables/d9-p5/README.md

# Precision 5680 D9 P5: 8-degree lean, drop-in contact pegs, finished edges

P5 is the D9 P2 no-metal-hardware dock with these changes and nothing else:

1. **8-degree lean and modular contact on the R7 frame.** Each cradle end is
   the R7 frame profile: base, brace, a tower whose top is the deck with two
   22-mm channels along the docking axis, the 8-degree lid rail (the only
   laptop-touching surface on the frame) and a 6-mm outer wall. Everything
   else the laptop touches is a drop-in peg on plate 08: a seat peg per
   machine (R2 seat with the V5 C relief) and a fence peg per end (64-mm
   underside wall at the plug end, 15-mm fence at the far end where the rear
   rubber-foot strip slides past during docking). One 36-mm fan pin pushed in
   from the outer face passes through the outer wall and both feet; the peg
   bores sit 0.15 mm lower than the frame bore so the pin cams both pegs onto
   the deck. Pull the pin and lift to swap pegs; push-out holes under the
   channels take a rod. Other machines: re-head the pegs, keep the frame. The
   plenum front wall moved from 24 to 26.5 mm so the 8-degree lid keeps 2 mm
   clearance at the top. The cradle base
   stays 4 mm so every foot remains coplanar with the ties.
2. **Fit corrections from the printed P2 fit plate.** Pin bores 8.8 -> 8.4 mm
   (now 0.5-mm diametral clearance on the 7.9-mm round pins); key barbs 6.2 ->
   7.2 mm wide through the 5.4-mm slot (total interference 0.8 -> 1.8 mm). The T
   tongue stays 12.7 mm tall: the P4 trim to 12.1 mm chased stuck support
   debris; the cleaned printed pair nests flush. One pin type (19 September):
   every pin, the 22 in the joints and the two peg locks, is a round 7.9-mm
   shaft with one chord flat on the bed, 0.5 mm diametral in the 8.4-mm bores.
   The printed P2 octagons (8.2 across corners, 7.6 across flats) rattled and
   the 18 September round 8.2-mm trial would not enter the printed bores;
   7.9 mm round was printed and confirmed to fit them on 19 September, so it is
   the production size. Any 8.2-mm trial pins from 18-19 September should be
   replaced from plate 07. Bonus fan-screw path (optional): the
   guards carry 4.5-mm clearance holes through plate and standoffs and every
   flange carries 3.5-mm blind pilots 6 mm deep on the fan's 105-mm pattern, so
   four M4 x 45 screws can hold guard and fan instead of (or as well as) the
   pins. The pilots are blind, so the air wall stays closed; plug or ignore
   them if unused. Shells printed before 18 September 17:00 lack the pilots:
   use the guard as a drill jig. Support-reducing gussets (18 September, no mating
   change; `check_no_removed_material.py` proves nothing was removed from any shell
   or guard): every external socket boss now carries a rib or a 34-degree wedge to
   the flange, and each seam tab carries a 34-degree wedge on its pin-tip end,
   which is the bed-facing end on the M1 inner shell and the M2 outer cradle. Those
   two parts lose 80 % and 64 % of their support road; the M1 outer cradle and
   M2 inner shell keep their tab towers because the pin head sits under those tab
   ends. The wedges add about 15 cm3 per plenum and 30 to 35 minutes of print time
   per gusseted shell, so the trade is cleanup for time. `overhang-threshold-test/`
   is the calibration: this Orca profile supports faces at 45 degrees from
   vertical and leaves 35 degrees alone.
3. **Splice ring (19 September).** The two inner halves stop 2.3 mm apart at
   the middle with nothing joining them and no laptop contact between the frame
   ends. Four clips now close a ring round the plenum section and lock the two
   halves to each other rather than resting on them. **The joint is one
   thickness**: each clip's tongue fills the whole 2.0-mm gap to full depth
   along the core of its arc, and steps down to half the gap only over the
   18-mm shiplap that straddles each junction, where the neighbour's opposite
   half makes the thickness back up. Every shiplap is trimmed against all four
   core bands, so it ends exactly where the neighbour's full-thickness core
   begins, with no overlap and no step. The assembled ring fills 4,923 mm3 of
   the 4,929 mm3 joint; the only voids are the four key clearances.
   **Flanges alternate**: the back clip laps the M1 half's skin, the front and
   floor clips lap M2's, so the ring holds both. The fan arc carries no flange:
   the fan mounting boss stands more than 5 mm proud of the plenum outline on
   that face of both halves, so there is no free skin to lap; the fan clip is
   held by its two end keys and by the neighbours it shiplaps into.
   **Neighbours engage**: every tongue is half
   the gap thick and sits on its own side of it, M2 clips low and M1 clips
   high, so adjacent arcs overlap as a half lap for 18 mm of run, and a 3-mm
   boss on each M2 clip passes through a socket in its M1 neighbour at all four
   junctions. A clip can only lift off the shell it laps by moving in the plane
   of the gap, which the keyed neighbours prevent. Junctions sit mid-face on
   the four longest runs of the section, never on a corner. The back clip also
   carries the hinge foot (bearing pad at the seat plane), the fence holder and
   a desk foot 0.5 mm above the four corner feet; the exchangeable
   `centre-fence` drops its 5.4-mm foot into that holder. Every piece prints
   flat with **zero support**, tongue and flange starting at the same bed face.
   The set is 11,400 mm3; in ASA the whole ring, the fence and the three
   glue-up keys slice at 13.24 g and 49 m 56 s with zero support. Epoxy it; the three alignment keys hold the
   halves square while it cures.
4. **Printable edge treatment.** Profile corners that run along each part's
   print Z are filleted (3 mm concave for stress relief, 1.5 mm convex for
   looks); the ties' top edges carry a 0.8-mm chamfer; bed edges are untouched.
   Every mating zone is protected and unchanged: air cavities, fan seats,
   blind sockets, pin bores, key slots, T joints, guard bars and standoffs,
   and the laptop contact band. Pins, keys and fit fixtures carry the P4
   fit corrections below.

Connections, plenum geometry, fan pose, guards and braces are P2. Two purchased
120 x 120 x 25 mm fans are still required. The plug mechanism is excluded.

## What to print

**Plate 09, the cradle-end trial**, is the M1 outer cradle sliced to its
16-mm frame width with a seat peg, the tall fence peg and a pin: print it
before the cradles to feel the 8-degree seat and the peg fit. Plates 02, 03,
05, 06 and 07 do not depend on the contact geometry.

Open **OPEN-ME.3mf** in OrcaSlicer; it is an identical copy of
**00-START-HERE-fastener-fit.3mf**, print only one of the two. Then print
plates **01 through 08 and 10 once each** for one dock: ten major parts, the four
splice clips and the exchangeable centre fence, three temporary alignment keys, four
pegs, 22 pins and 20 locking keys. Each numbered 3MF contains
one frozen, named plate with matching embedded G-code; matching standalone
G-code, oriented STL and assembly-coordinate STEP bodies are included. The
STL poses are intentional; do not auto-orient them. Print the two outer
cradle plates (01 and 04) after the plate 09 trial; the other five plates do
not depend on the contact geometry.

Printer/profile: Repro Bambu P1S, 0.4 mm nozzle, Generic PETG Starter,
textured PEI, 0.2 mm layers, five walls, six top/bottom layers, 5 mm brim,
40 % gyroid on the main plates and 100 % on the fasteners. Supports are
enabled for accessible hidden surfaces. Confirm the actual printer and
filament before using the saved G-code.

## Parts and identification

| Pin use | Quantity | Head-edge notches | Shaft length | Matching key |
| --- | ---: | ---: | ---: | --- |
| Fan guards | 8 | 1 | 36 mm | Six long; two short at the outboard lower sockets |
| Frame ends | 4 | 2 | 32.8 mm | Long |
| Plenum seams | 6 | 3 | 26 mm | Long |
| Brace T joints | 2 | 4 | 29.4 mm | Short |

There are 16 long keys (22.5 mm overall, 16 mm grip) and four short keys
(15.5 mm overall, 8 mm grip). Each pin has an additional 4 mm head. Part
names are retained in the Orca projects and CAD files.

## Assembly

1. Remove supports and brim while the shell halves are open. Clean pin bores
   and key windows without enlarging their bearing surfaces.
2. Join each front/rear brace on the bench: lower the male T tongue into the
   floor-backed female pocket, insert a four-notch pin, then its short key.
   The complete brace attaches to the cradle feet with two-notch pins and
   long keys.
3. Dry-fit each matching M1/M2 shell pair. Join its three internal tabs with
   three-notch pins and long keys before fitting the fans. The rear-wall seam
   key inserts downward through the open mouth. Optional thin seam sealant
   addresses physical leakage; it is not the structural connection.
4. Place each fan against its flange and add the guard. Four one-notch pins
   run outside the fan frame into blind sockets; factory screw holes are
   unused. The lower outboard sockets take short keys from the outer cradle
   side; rotate those pins a quarter-turn so the cross-slot faces that side.
5. To service a rear brace T joint, remove the complete brace from the cradle
   feet first. Remove fans before servicing the internal plenum retainers.

## Verification and limits

All 64 assembly solids are valid, single-component watertight meshes. No
nominal volume interference exists between assembly parts, purchased fan
envelopes or the upper laptop envelope. Pin/key insertion was re-checked at
five positions along each path with compressed key-barb geometry. Both
plenums pass the nominal enclosure checks with the two actual shell halves
and each named port capped in turn, and the edge treatment changed the
intended air volume of each module by exactly zero. Every plate passed the
native Orca verification: unchanged poses and placement, all roads inside the
usable bed and outside the exclusion zone, expected heights, matching
embedded and standalone G-code, and per-object support and bridge counts
recorded (hidden supports on shells, guards and ties are intended).

This is a prototype print kit. Physical seating of the R4-C cradles, pin/key
fit, support removal, loaded stability, creep, retention durability, cooling
and acoustics remain untested. No 800 RPM performance claim is made.

## Editable source and provenance

`source/build_d9.py` runs with CadQuery 2.8, trimesh, Shapely and Pillow, with
`source/dress.py` for the edge treatment. The frozen R4-C cradle source
(`source-inputs/quick-fit/R7`, built from the R2 bracket by the R7 builder with
`--variant C --base-thickness 4 --tag d9-source`), the R2 inputs and the
geometry JSON are included. STEP files preserve assembled coordinates; STL
files preserve print poses. Preparation helpers and frozen profiles are
included. SHA256.json and the ZIP payload are verified against the standalone
print directory.
