thereprocase/5680-dock/desk-dock/D7/D7-assembled.png

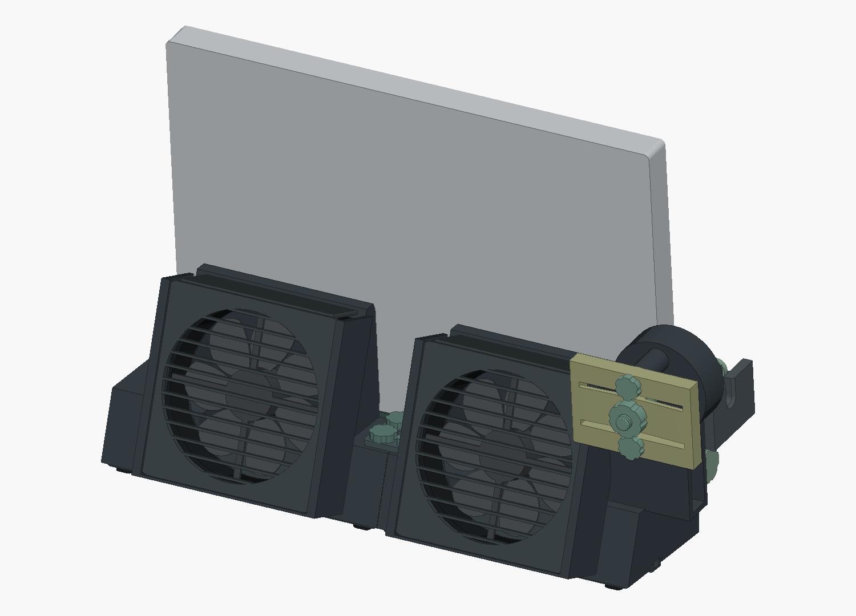
desk-dock/D7/D7-assembled.png
