thereprocase/5680-dock/desk-dock/D8/quick-fit/R6/D8-R6-assembled.png

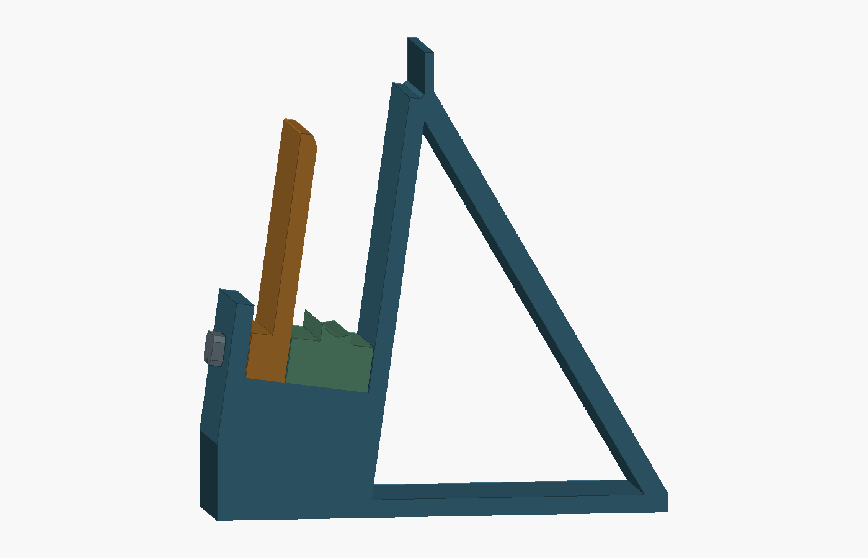
desk-dock/D8/quick-fit/R6/D8-R6-assembled.png
