thereprocase/5680-dock/desk-dock/D9-P5/clamp-pivot-views/01-assembled-port-1.png

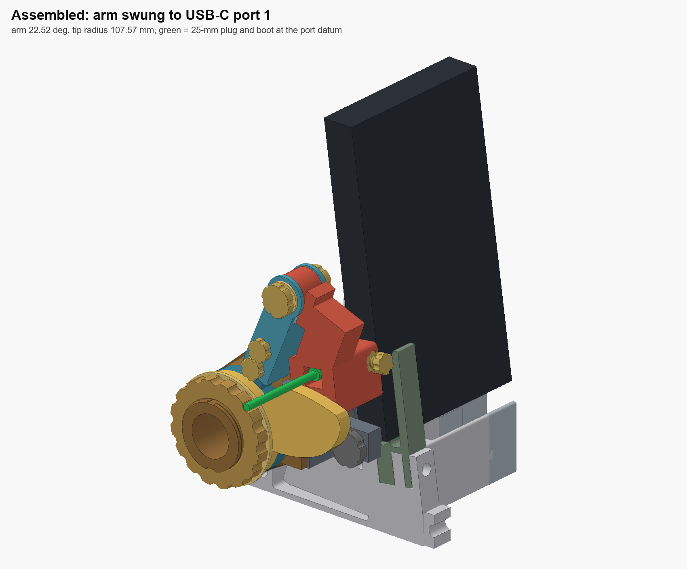
desk-dock/D9-P5/clamp-pivot-views/01-assembled-port-1.png
