thereprocase/5680-dock/desk-dock/D9-P5/clamp-pivot-views/02-assembled-end-view.png

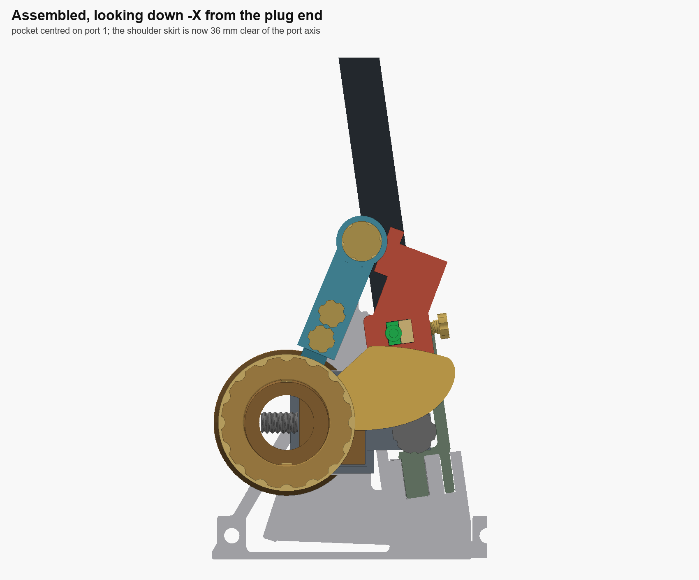
desk-dock/D9-P5/clamp-pivot-views/02-assembled-end-view.png
