thereprocase/5680-dock/docs/printables/d9-p1/D9-P1-assembly.png

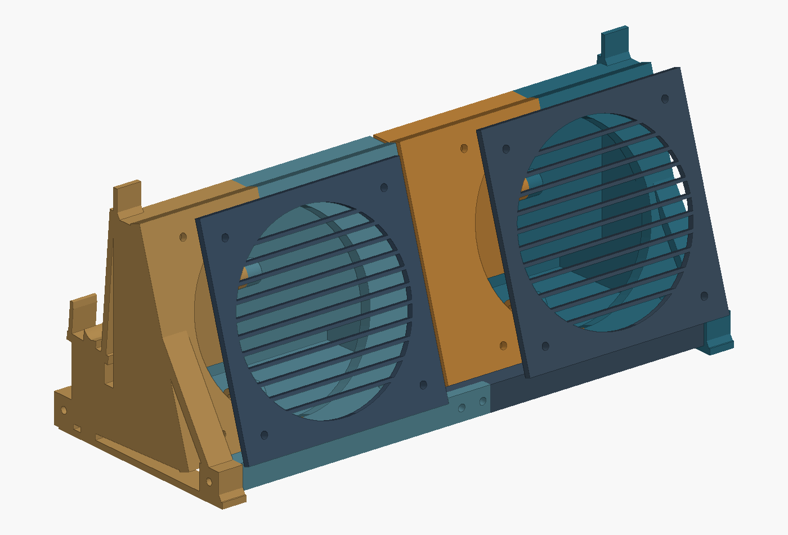
docs/printables/d9-p1/D9-P1-assembly.png
