thereprocase/5680-dock/docs/printables/d9-p2/D9-P2-assembly.png

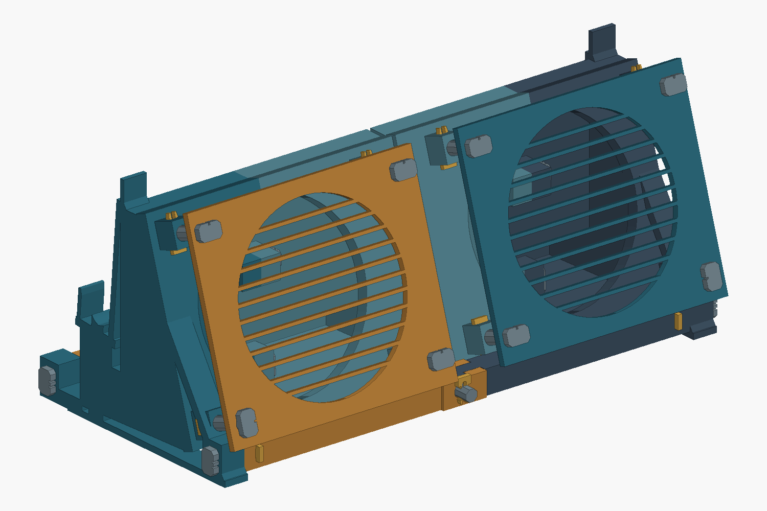
docs/printables/d9-p2/D9-P2-assembly.png
