thereprocase/5680-dock/docs/printables/d9-p2/D9-P2-key-toolpaths.png

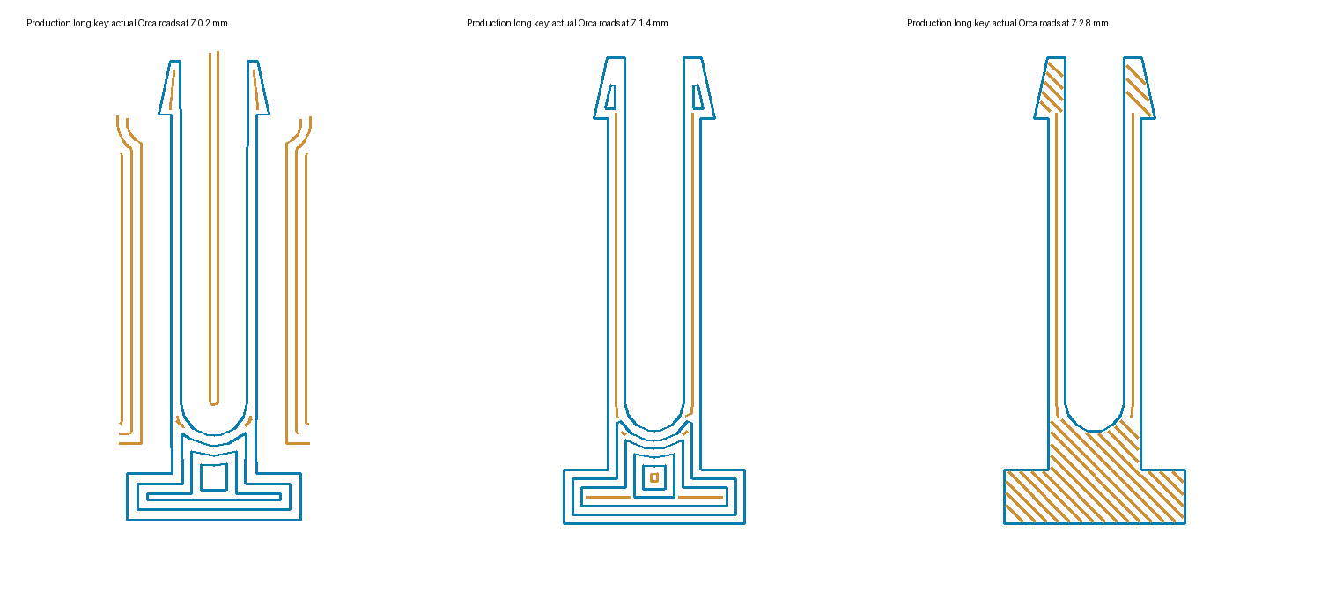
docs/printables/d9-p2/D9-P2-key-toolpaths.png
