thereprocase/5680-dock/docs/printables/d9-p3/preview-M1-outer-cradle-dressed.png

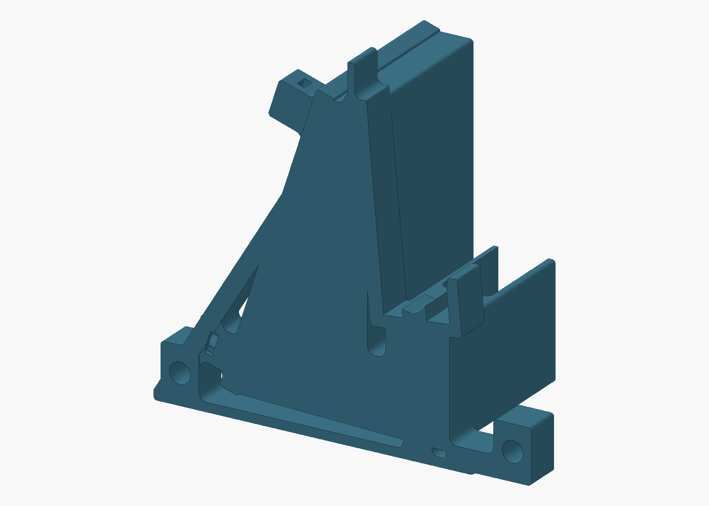
docs/printables/d9-p3/preview-M1-outer-cradle-dressed.png
