thereprocase/5680-dock/docs/printables/d9-p5/D9-P5-assembly.png

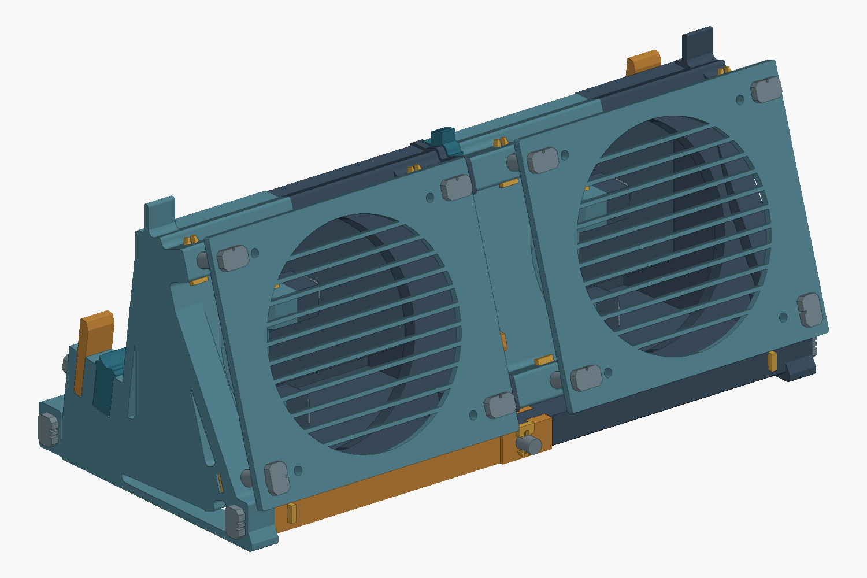
docs/printables/d9-p5/D9-P5-assembly.png
