thereprocase/5680-dock/desk-dock/D9-P5/overhang-threshold-test/actual-toolpaths.png

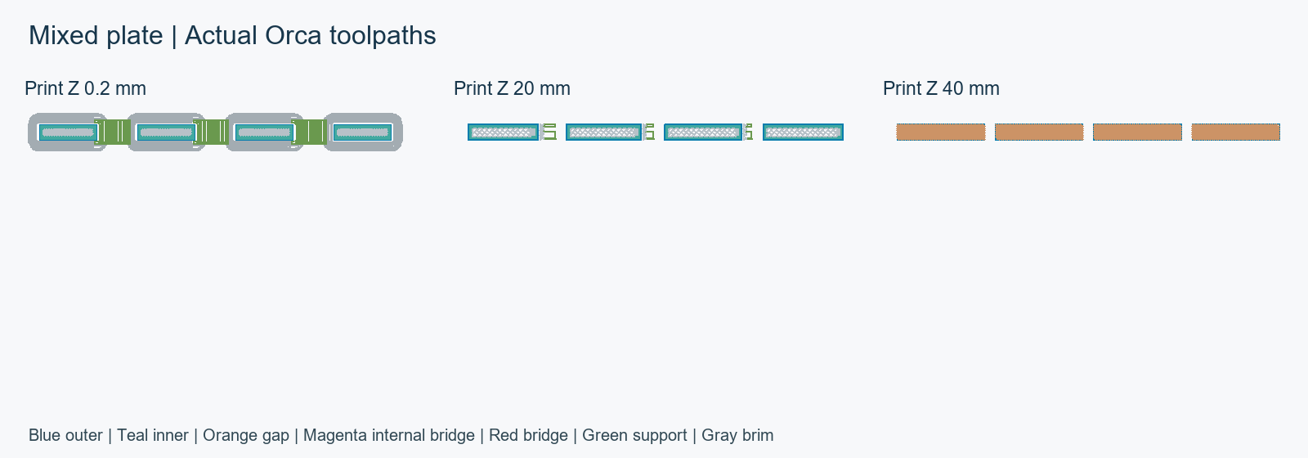
desk-dock/D9-P5/overhang-threshold-test/actual-toolpaths.png
