thereprocase/5680-dock/desk-dock/history/32361.jpg

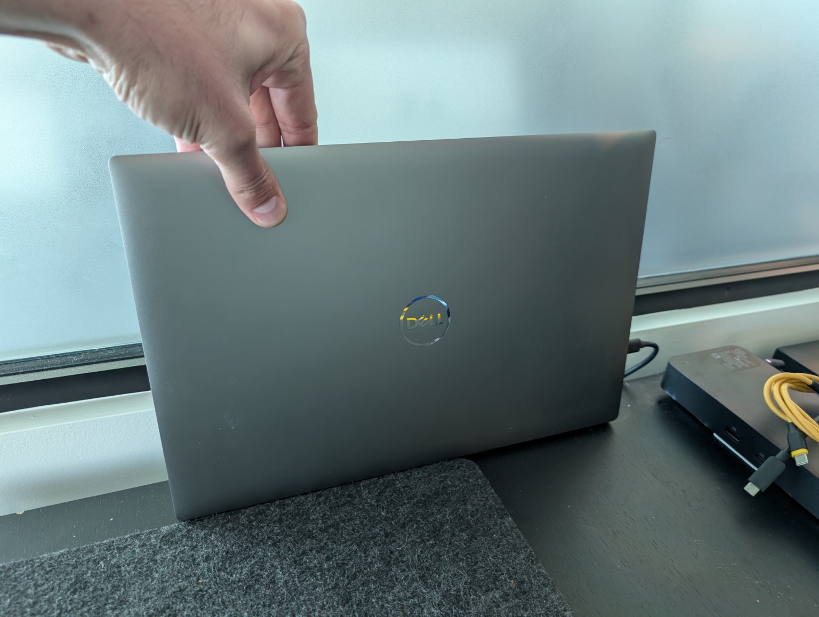
desk-dock/history/32361.jpg
