thereprocase/5680-dock/desk-dock/history/reference-assets/left.jpg

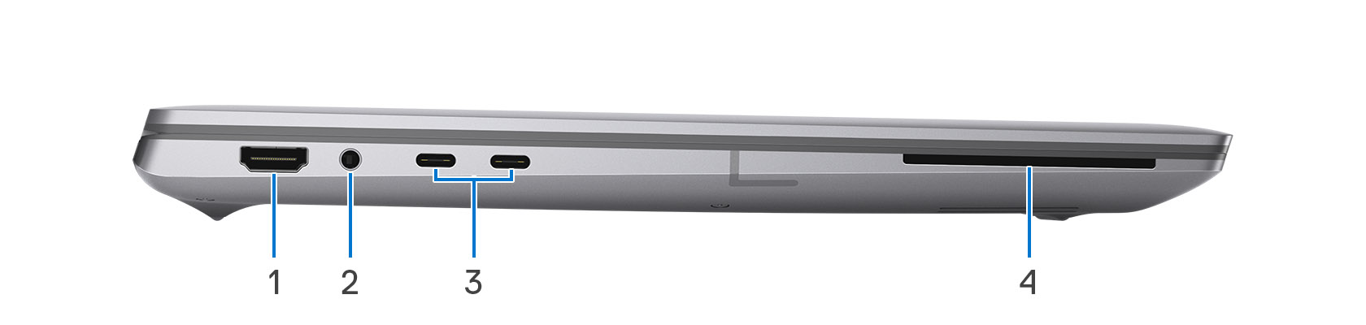
desk-dock/history/reference-assets/left.jpg
