thereprocase/5680-dock/desk-dock/history/remove-end-tab.png

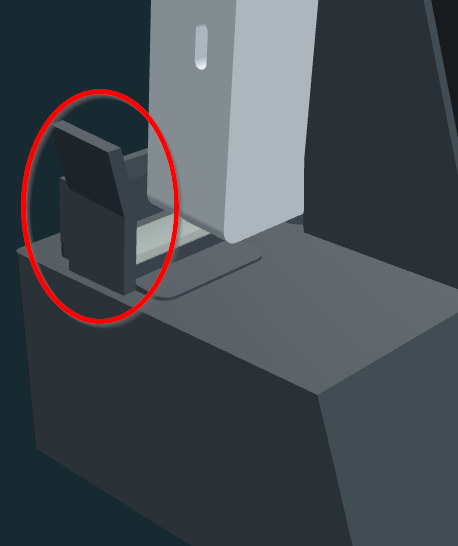
desk-dock/history/remove-end-tab.png
