thereprocase/5680-dock/desk-dock/history/simplification-request.png

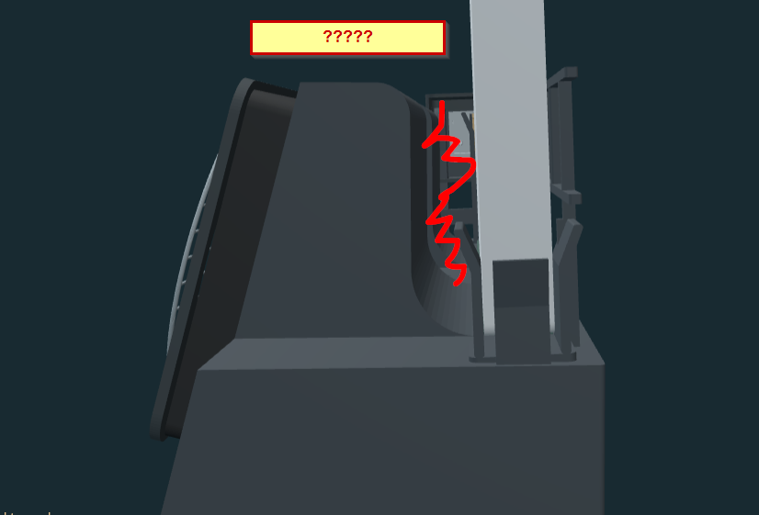
desk-dock/history/simplification-request.png
